om7ea/B737/docs/models/35-cabin-alt-diff-press-gauge.md

# 35. Cabin Alt / Diff Press Gauge

[📦 Download the printable model on MakerWorld](https://makerworld.com/en/models/3334561-boeing-737-overhead-cabin-alt-diff-press-gauge)

[← Back to model list](README.md)

---

> **Note**
> This gauge is a model of its own - it is not part of any panel model. **One** is needed for the complete project, on the **[Cabin Altitude Panel](36-cabin-altitude-panel.md)**.
>
> It is a **two-needle** instrument, and the largest gauge of the overhead. Both needles turn on the same axis, the short CABIN ALT needle on an acrylic pipe and the long DIFF PRESS needle on an acrylic rod running inside that pipe, and each one has a servo of its own.

---

## Photos

<table>
<tbody>
<tr>
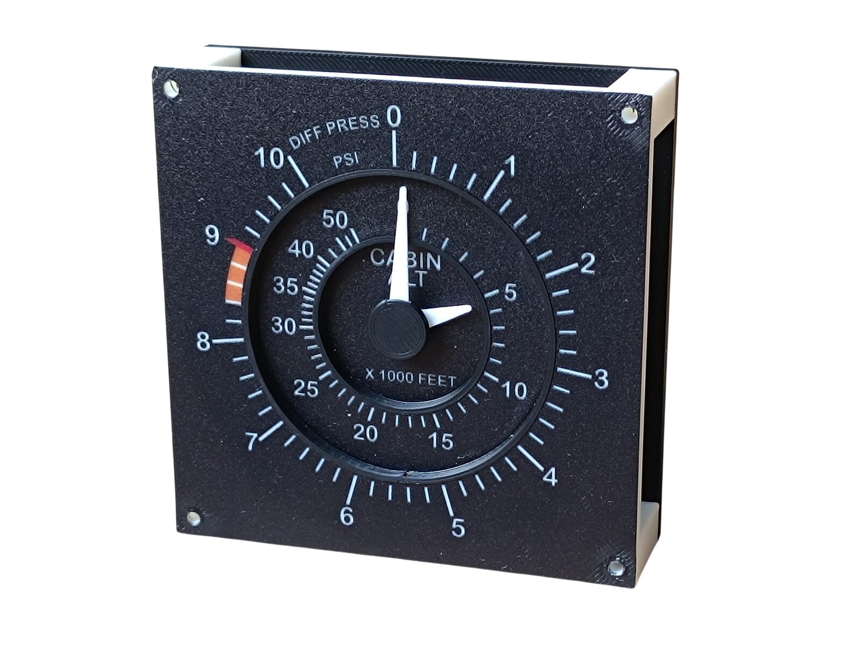
[picture p176: images/panels/35-cabin-alt-photo-1-front.jpg]
Finished Cabin Alt / Diff Press Gauge, front
<td align="center" width="50%"><br><sub>The finished gauge</sub></td>
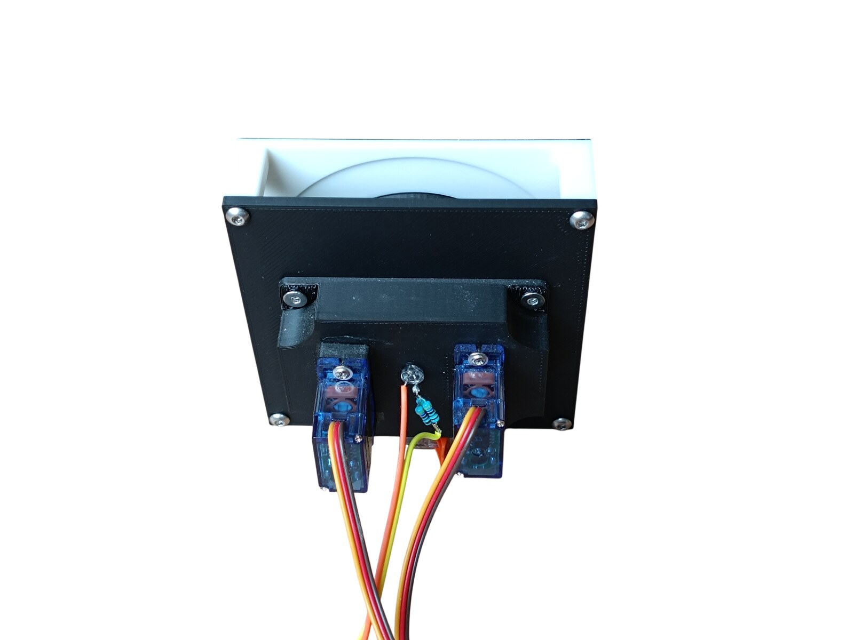
[picture p177: images/panels/35-cabin-alt-photo-2-rear.jpg]
The gauge from behind, showing the two servos on the gears cover and the resistor of the needle LED
<td align="center" width="50%"><br><sub>From behind - the two servos on the gears cover, with the resistor of the needle LED between them</sub></td>
</tr>
</tbody>
</table>

---

## How It Works

The dial is built from three printed faces, one behind the other, each with its own UV-printed scale: the square **outer** face carries the **DIFF PRESS** scale in psi, the **middle** ring the **CABIN ALT** scale in thousands of feet, and the **inner** disc the CABIN ALT lettering. A black shielding ring sits between each pair, so no light crosses from one face to the next.

Each needle is driven by its own **SG90 servo** through a pair of printed gears. The **18-tooth** gear sits on the servo and a **9-tooth** gear on the needle shaft, so a needle turns twice as far as its servo - the 180° of an SG90 cover the whole scale.

The two shafts run on the same axis, one inside the other. The **short needle**, the one that reads CABIN ALT, sits on a **3 mm acrylic pipe** turning in two **MR63ZZ** ball bearings, one in the inner part and one in the backlight part. The **long needle**, the one that reads DIFF PRESS, sits on a **2 mm acrylic rod** that runs down the middle of that pipe; at the back the rod turns in a single **MR52ZZ** bearing pressed into the pipe gear, and at the front the pipe itself guides it.

What keeps the two drives apart is height. The two servos sit at different depths in the gears cover, and the two gears on the shafts are different heights as well - the **3 mm pipe gear** and the **2 mm rod gear** - so each servo gear reaches only one of them.

Both shafts are light pipes too: a white LED in the gears cover shines up the rod and the pipe into the needles. The two gears at the back sit in that light path, which is why they are printed in **transparent** PLA.

The dial itself is lit separately, by two LED strips inside the backlight part - see [Backlight](#backlight).

---

## Filament

| | Colour | Filament |
|---|---|---|
|  | Transparent | Filament PM PLA Transparent |
|  | White | Bambu PLA Basic Jade White (10100) |
|  | Black | Bambu PLA Basic Black (10101) |

---

## 3D Printed Parts

| Qty | Part | Colour | Notes |
|---:|---|---|---|
| 1× | outer | White | the square face - the UV-printed DIFF PRESS scale goes on it and it diffuses the backlight |
| 1× | middle | White | the ring behind it, with the UV-printed CABIN ALT scale |
| 1× | inner | White | the disc at the centre, with the CABIN ALT lettering; carries the first MR63ZZ bearing |
| 1× | shielding outer+middle | Black | the ring wall between the outer and the middle face |
| 1× | shielding middle+inner | Black | the ring wall between the middle and the inner face |
| 1× | backlight | Black | the rear plate; carries the second MR63ZZ bearing |
| 1× | gears cover | Black | the bracket for the two servos |
| 1× | pipe gear (3 mm) | Transparent | 9 teeth, on the acrylic pipe; in the light path of the needle LED |
| 1× | rod gear (2 mm) | Transparent | 9 teeth, on the acrylic rod; in the light path of the needle LED |
| 2× | servo gear | Black | 18 teeth, on the servo shafts |
| 1× | long needle | White | the DIFF PRESS needle, on the acrylic rod |
| 1× | short needle | White | the CABIN ALT needle, on the acrylic pipe |
| 1× | needle cap | Black | covers the hub of the long needle |

All the parts print on a **Smooth** PEI plate.

---

## Electronic and Mechanical Components

| Qty | Part | Reference |
|---:|---|---|
| 2× | **Servo SG90** - 180°, plastic gears | [Product I used](../../images/parts/AE_servo_SG90.png) |
| 2× | **Ball bearing MR63ZZ** - 3 × 6 × 2.5 mm | [Product I used](../../images/parts/AE_bearing_MR63ZZ.png) |
| 1× | **Ball bearing MR52ZZ** - 2 × 5 × 2.5 mm | [Product I used](../../images/parts/AE_bearing_MR52ZZ.png) |
| 1× | **Acrylic pipe** - 2.1 × 3 × 200 mm, transparent; the shaft of the short needle is cut from it | [Product I used](../../images/parts/AE_acrylic_pipe.png) |
| 1× | **Acrylic rod** - 2 mm, transparent; the shaft of the long needle is cut from it | [Product I used](../../images/parts/AE_acrylic_rod.png) |
| 1× | **White 5 mm flat top LED** - the same one the annunciators use | [Product I used](../../images/parts/AE_led_white.png) |
| 1× | **150 Ω resistor** - in series with the white LED | |
| 2× | **LED strip** - the scale backlight | [Product I used](../../images/parts/AE_led_strip.png) |
| 1× | **820 Ω resistor** - in series with the two LED strips | |
| 2× | **Splice connector** - lever type, for the 12 V of the scale backlight | |

The screws that come with the servos are used as well: two hold each servo to the gears cover, and a third fastens its gear to the servo shaft.

---

## Screws

| Qty | Screw | Joins |
|---:|---|---|
| 4× | Dome head M3×8 | backlight + outer |
| 4× | Dome head M3×5 | gears cover + backlight |

---

## UV Print Files

| Qty | File |
|---:|---|
| 1× | A4 PDF - gauge scales |

Three of the scales on that sheet belong to this gauge: the large square **DIFF PRESS** face, the **CABIN ALT** ring with the numbers, and the small disc with the CABIN ALT lettering. The PDF and the printing instructions are on the [UV Print Files](../uv-print.md) page.

---

## Backlight

### Scale

The scale is lit by two LED strips inside the backlight part, one on each side, shining through the white outer, middle and inner parts from behind. They run on **12 V** taken from the backlighting of the [Cabin Altitude Panel](36-cabin-altitude-panel.md), so the gauge dims together with that panel - see [Power supply](../system-overview.md#power-supply).

The two strips are not wired straight across that 12 V: an **820 Ω resistor** goes in series with the pair. The white parts pass far more light than the printed face of a panel does, so on the bare supply the scale burns out much brighter than the lettering around it. The resistor holds it back to the brightness of the rest of the overhead.

The two strips sit in parallel and the resistor goes in the lead feeding them, close to the strips.

The two LED strips in parallel with the series resistor in the supply lead

### Needles

The needles have a light of their own: a white 5 mm LED in the gears cover, between the two servos, shining up through the transparent gears and on into the acrylic pipe and the acrylic rod. It runs on **5 V** with a **150 Ω** resistor in series, and it lights both needles at once.

> **Note**
> The needle lighting works, but the effect is weak. White PLA does not carry light well over the length of a needle, so a needle glows rather than lights up. It is worth building - but do not expect the needles to stand out the way the scale does.

---

## Wiring

The gauge has four connections.

| Connection | Supply | Comes from |
|---|---|---|
| CABIN ALT needle servo | 5 V | the control signal, **+5 V** and **GND**, all three from the pin headers at **pin 7** of the [RJ45 Direct](../pcb/rj45-direct.md) PCB on the **[Cabin Altitude Panel](36-cabin-altitude-panel.md)** - socket **D3** on **Overhead_4** |
| DIFF PRESS needle servo | 5 V | the same three, from the pin headers at **pin 6** of that board |
| Needle LED | 5 V | **+5 V** and **GND** from a two-pin header on that same board - see [the modified board](36-cabin-altitude-panel.md#the-modified-board). The pair runs through a **150 Ω** resistor - see [Backlight](#backlight) |
| Scale backlight | 12 V | the backlighting of the Cabin Altitude Panel, through an **820 Ω** resistor - see [Backlight](#backlight) |

> **⚠️ Both servo plugs have to be rewired**\
> The SG90 does not leave the factory in the order the RJ45 Direct PCB expects, so a servo will **not** work if you plug it in as it comes. **Swap the red and the yellow wire:**
>
> | | Wire order in the plug |
> |---|---|
> | As delivered | brown - red - yellow |
> | **Needed** | **brown - yellow - red** |
>
> Lift the small tabs on the plastic housing, pull those two crimped contacts out and swap them over. Brown stays where it is. (On some SG90s the yellow wire is orange instead - it is the signal wire either way.)

The 12 V for the scale backlight is brought over from the panel's own backlighting with two **lever-type splice connectors**, one for +12 V and one for GND. Where they sit is up to you - both on the gauge works fine, and so does one on the gauge and one on the panel. There is nothing to screw them to, so **glue them down with super glue.**

---

## Assembly

Screw abbreviations used below: **DH** = dome head.

<table>
<tbody>
<tr>
<td width="55%"><b>1.</b> Screw the two servos to the <b>gears cover</b> with the screws that come in the servo bags, two per servo.</td>
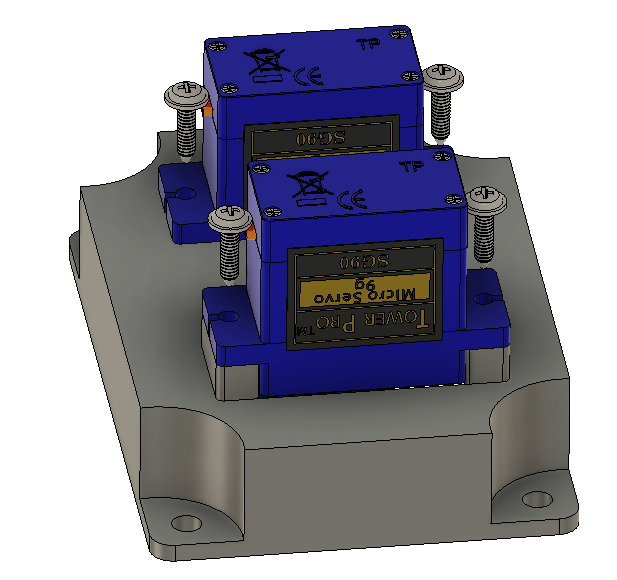
[picture p178: images/panels/35-cabin-alt-step-01.png]
The two servos screwed to the gears cover
<td align="center"></td>
</tr>
</tbody>
<tbody>
<tr>
<td width="55%"><b>2.</b> Fasten an 18-tooth <b>servo gear</b> to each servo, again with a screw from the servo bag.</td>
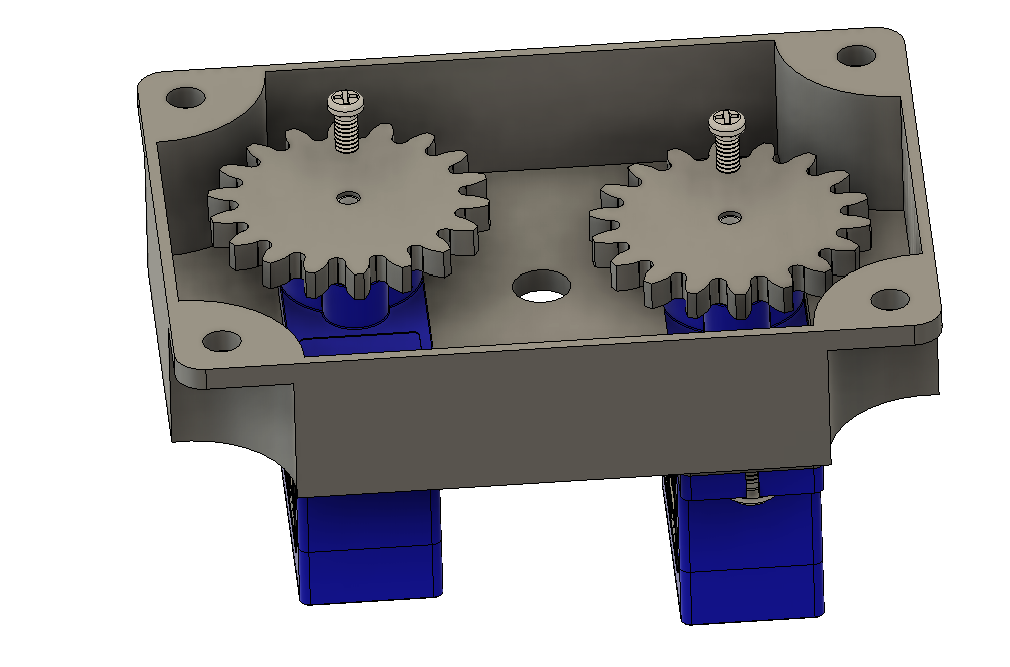
[picture p179: images/panels/35-cabin-alt-step-02.png]
The 18-tooth gears fastened to the servo shafts
<td align="center"></td>
</tr>
</tbody>
<tbody>
<tr>
<td width="55%"><b>3.</b> Stick the printed foil with the <b>DIFF PRESS</b> scale onto the <b>outer</b> part.</td>
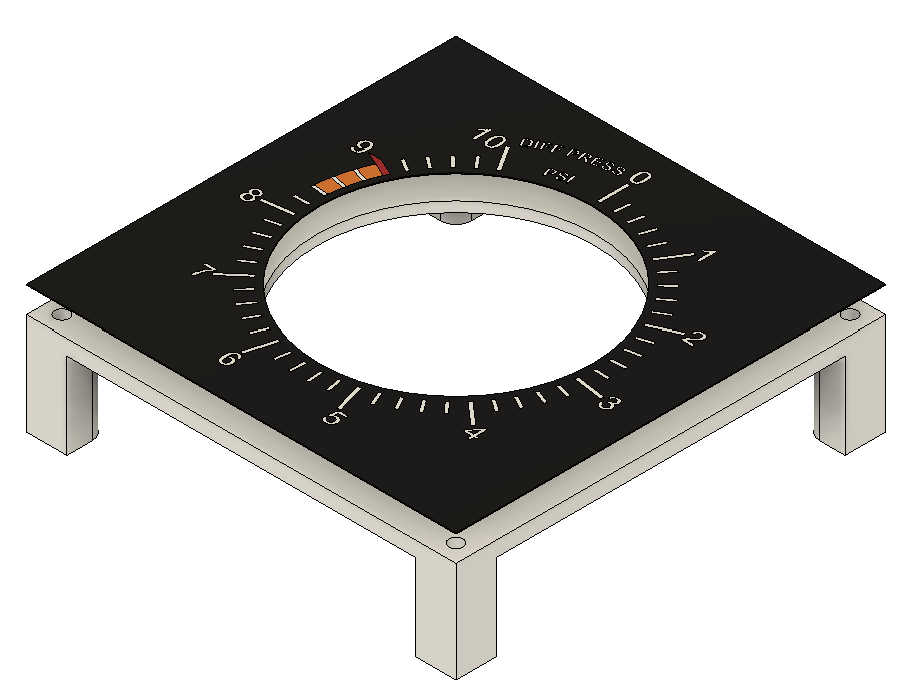
[picture p180: images/panels/35-cabin-alt-step-03.png]
The DIFF PRESS foil stuck onto the outer part
<td align="center"></td>
</tr>
</tbody>
<tbody>
<tr>
<td width="55%"><b>4.</b> Stick the printed foil with the <b>CABIN ALT</b> scale onto the <b>middle</b> part.</td>
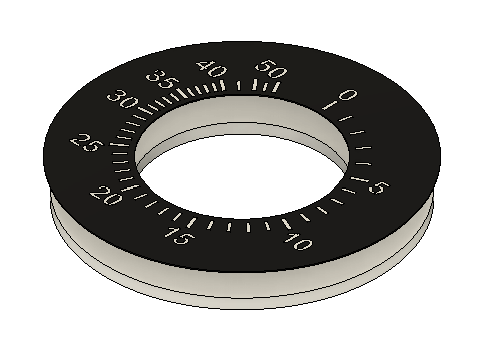
[picture p181: images/panels/35-cabin-alt-step-04.png]
The CABIN ALT scale foil stuck onto the middle part
<td align="center"></td>
</tr>
</tbody>
<tbody>
<tr>
<td width="55%"><b>5.</b> Stick the printed foil with the CABIN ALT lettering onto the <b>inner</b> part.</td>
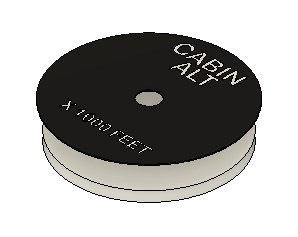
[picture p182: images/panels/35-cabin-alt-step-05.png]
The lettering foil stuck onto the inner part
<td align="center"></td>
</tr>
</tbody>
<tbody>
<tr>
<td width="55%"><b>6.</b> Drop the <b>shielding outer+middle</b> part into the outer part.</td>
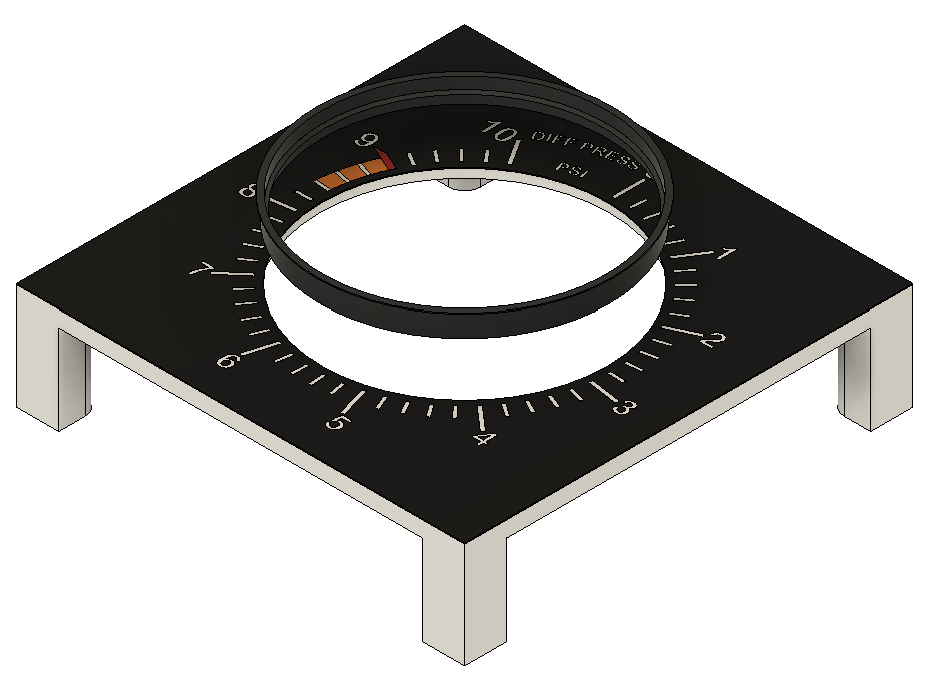
[picture p183: images/panels/35-cabin-alt-step-06.png]
The outer shielding ring dropped into the outer part
<td align="center"></td>
</tr>
</tbody>
<tbody>
<tr>
<td width="55%"><b>7.</b> Drop the <b>middle</b> part into that shielding.</td>
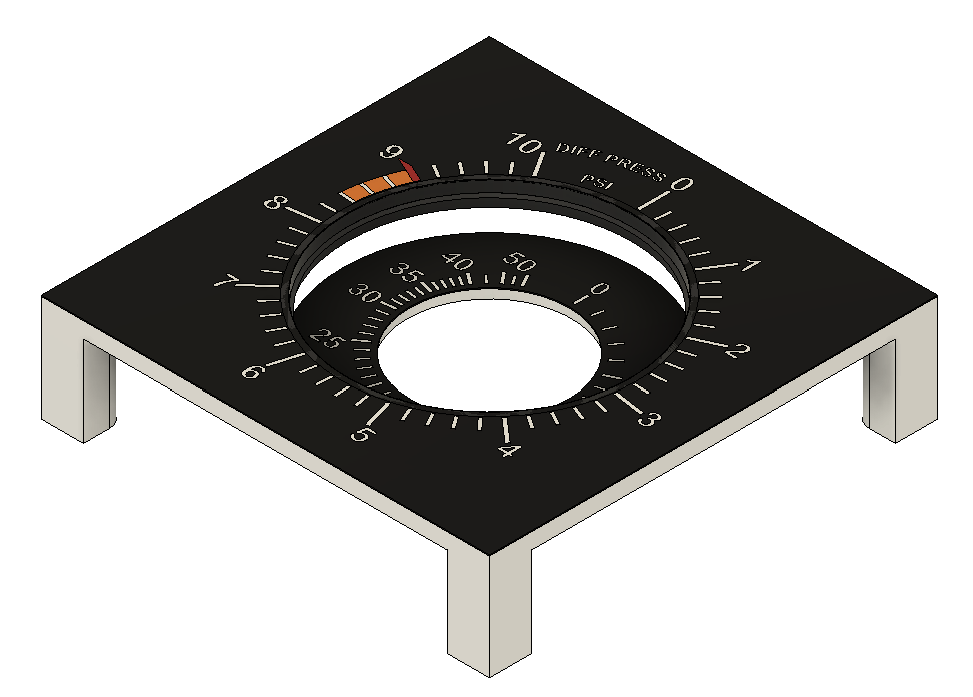
[picture p184: images/panels/35-cabin-alt-step-07.png]
The middle part dropped into the outer shielding ring
<td align="center"></td>
</tr>
</tbody>
<tbody>
<tr>
<td width="55%"><b>8.</b> Drop the <b>shielding middle+inner</b> part in next.</td>
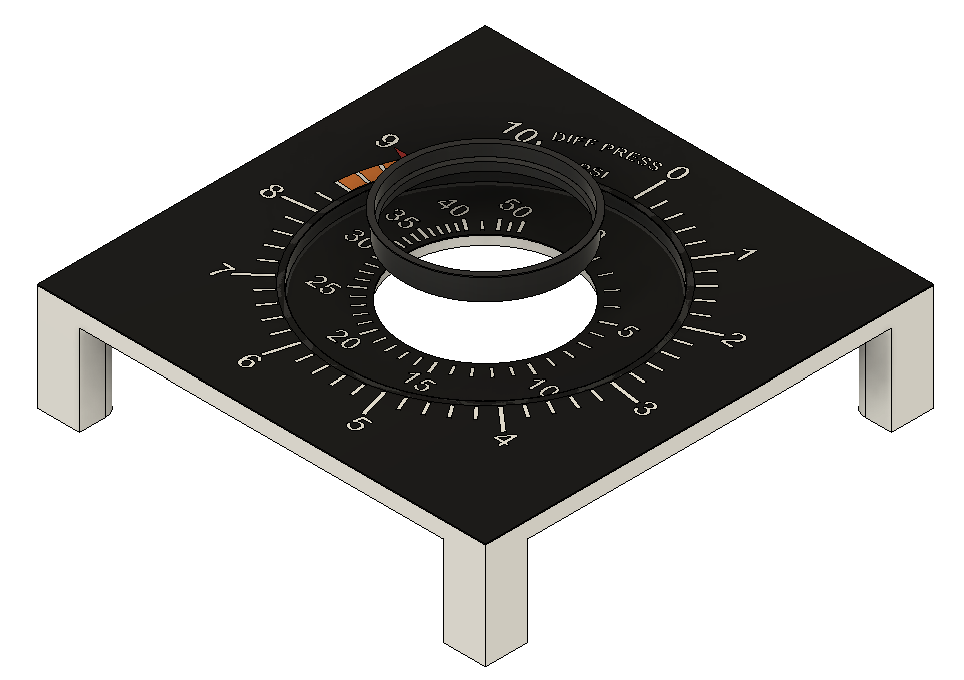
[picture p185: images/panels/35-cabin-alt-step-08.png]
The inner shielding ring dropped in
<td align="center"></td>
</tr>
</tbody>
<tbody>
<tr>
<td width="55%"><b>9.</b> Drop the <b>inner</b> part into it.</td>
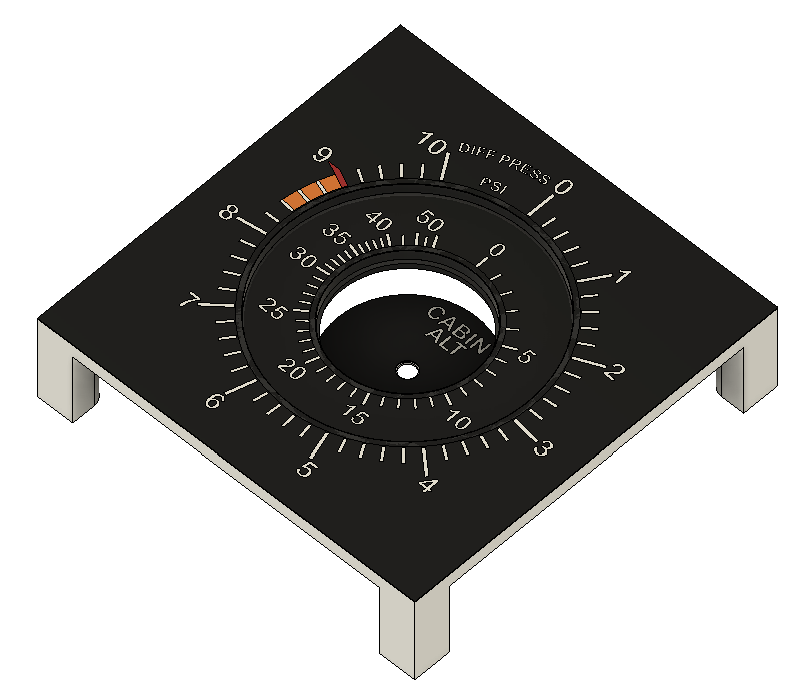
[picture p186: images/panels/35-cabin-alt-step-09.png]
The inner part dropped into the inner shielding ring
<td align="center"></td>
</tr>
</tbody>
<tbody>
<tr>
<td width="55%"><b>10.</b> Press the first <b>MR63ZZ</b> bearing into the inner part, from the back.</td>
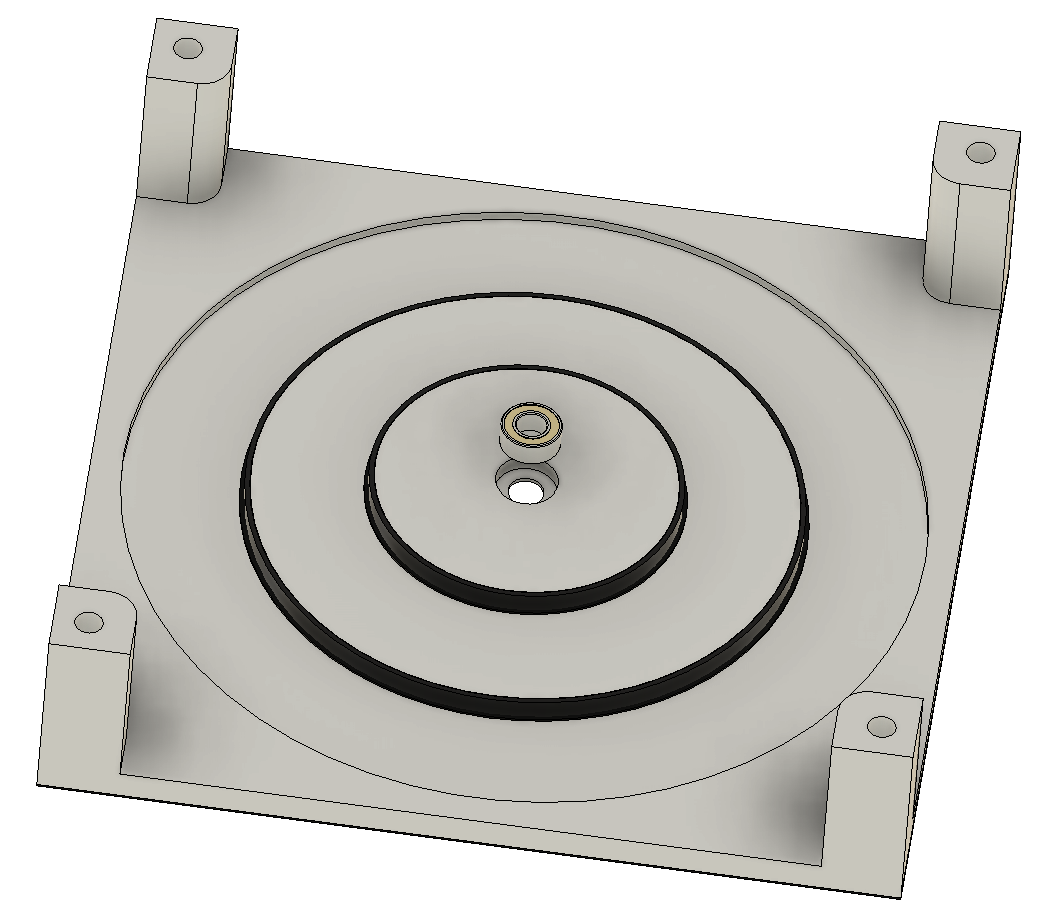
[picture p187: images/panels/35-cabin-alt-step-10.png]
The first MR63ZZ bearing pressed into the inner part
<td align="center"></td>
</tr>
</tbody>
<tbody>
<tr>
<td width="55%"><b>11.</b> Fit the two <b>LED strips</b> into the <b>backlight</b> part and bring their leads out. The two are wired in parallel and the <b>820 Ω resistor</b> goes in the lead feeding them - see <a href="#backlight">Backlight</a>. They have to go in before the part is screwed on in the next step.</td>
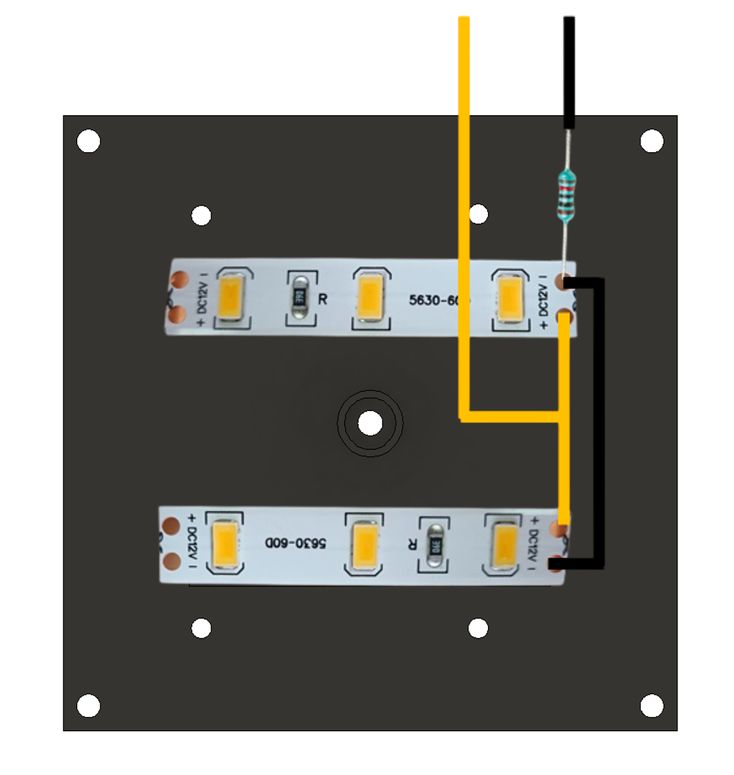
[picture p188: images/panels/35-cabin-alt-backlight-leds.png]
The two LED strips on the backlight part, wired in parallel with the series resistor
<td align="center"></td>
</tr>
</tbody>
<tbody>
<tr>
<td width="55%"><b>12.</b> Screw the <b>backlight</b> part on with 4× DH M3×8.</td>
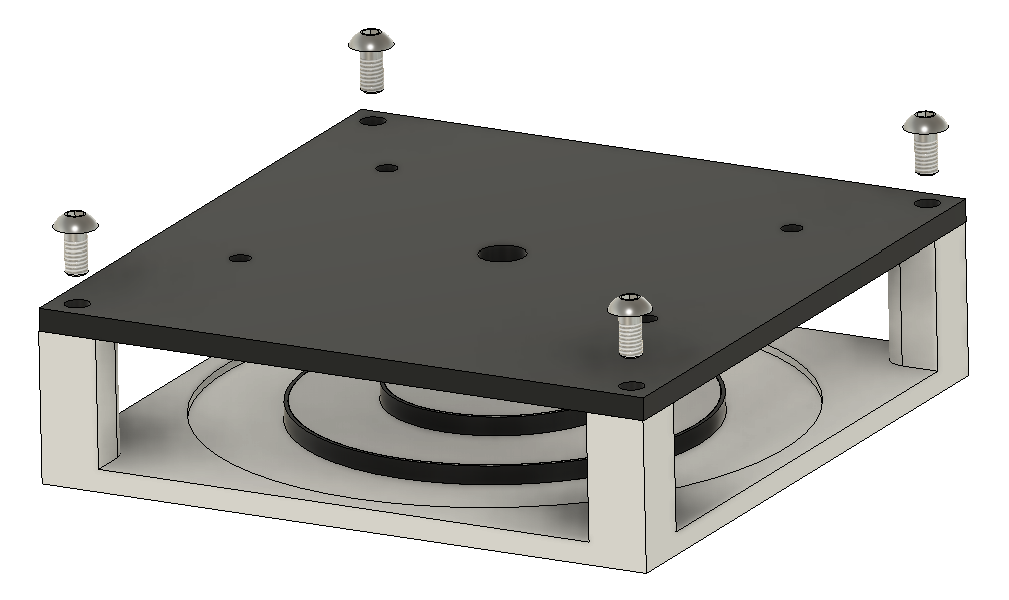
[picture p189: images/panels/35-cabin-alt-step-12.png]
The backlight part screwed on with four M3x8 screws
<td align="center"></td>
</tr>
</tbody>
<tbody>
<tr>
<td width="55%"><b>13.</b> Press the second <b>MR63ZZ</b> bearing into the backlight part.</td>
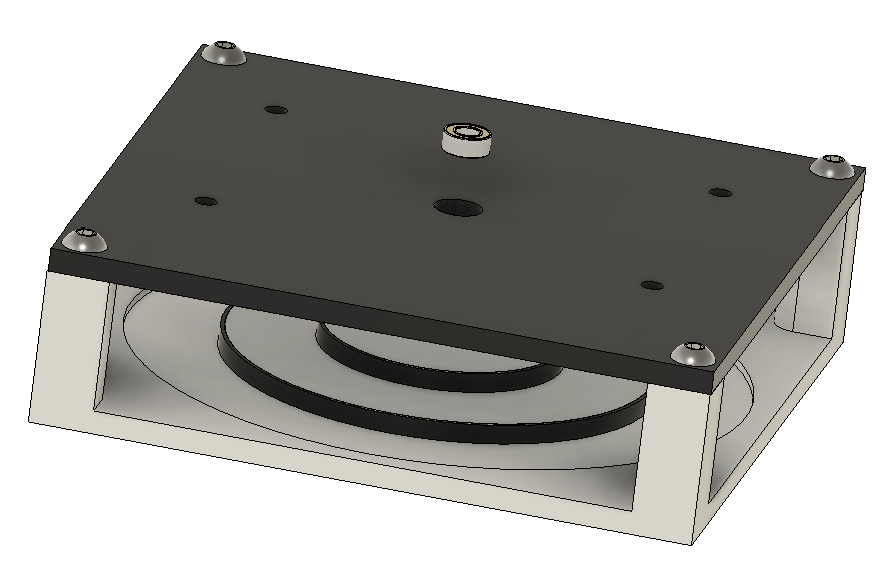
[picture p190: images/panels/35-cabin-alt-step-13.png]
The second MR63ZZ bearing pressed into the backlight part
<td align="center"></td>
</tr>
</tbody>
<tbody>
<tr>
<td width="55%"><b>14.</b> Push the <b>acrylic pipe</b> through both bearings. If it will not go, warm it with a hair dryer to soften it slightly. I used a 23.5 mm length.</td>
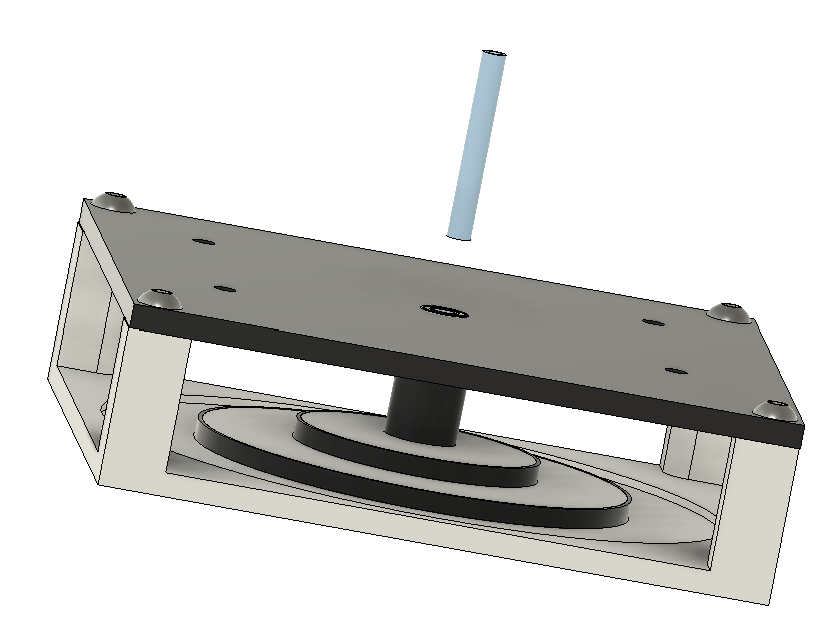
[picture p191: images/panels/35-cabin-alt-step-14.png]
The acrylic pipe pushed through both bearings
<td align="center"></td>
</tr>
</tbody>
<tbody>
<tr>
<td width="55%"><b>15.</b> From the front, glue the <b>short needle</b> - the CABIN ALT one - onto the pipe with super glue.</td>
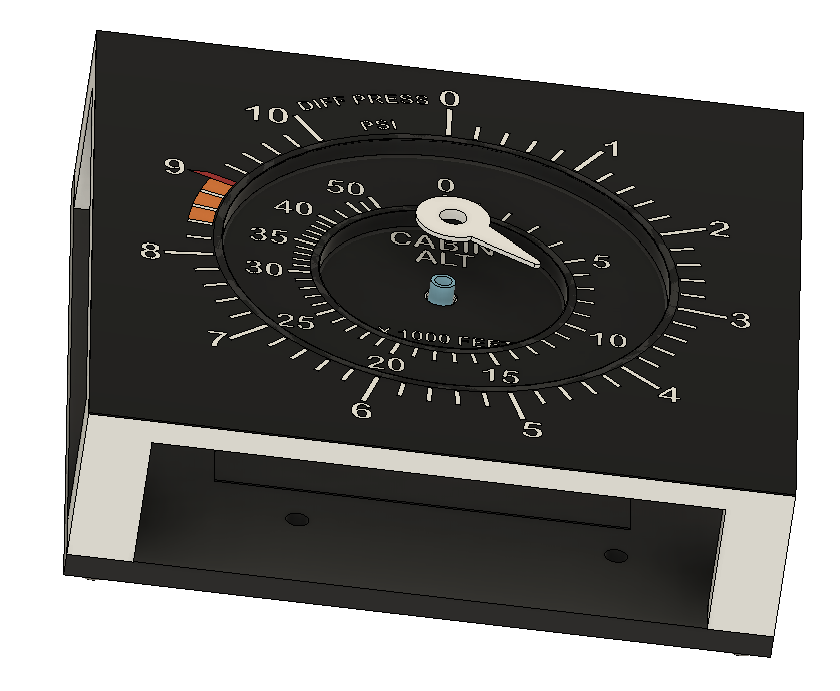
[picture p192: images/panels/35-cabin-alt-step-15.png]
The short needle glued onto the acrylic pipe from the front
<td align="center"></td>
</tr>
</tbody>
<tbody>
<tr>
<td width="55%"><b>16.</b> From the back, glue the <b>pipe gear</b> - 9 teeth, 3 mm high - onto the acrylic pipe.</td>
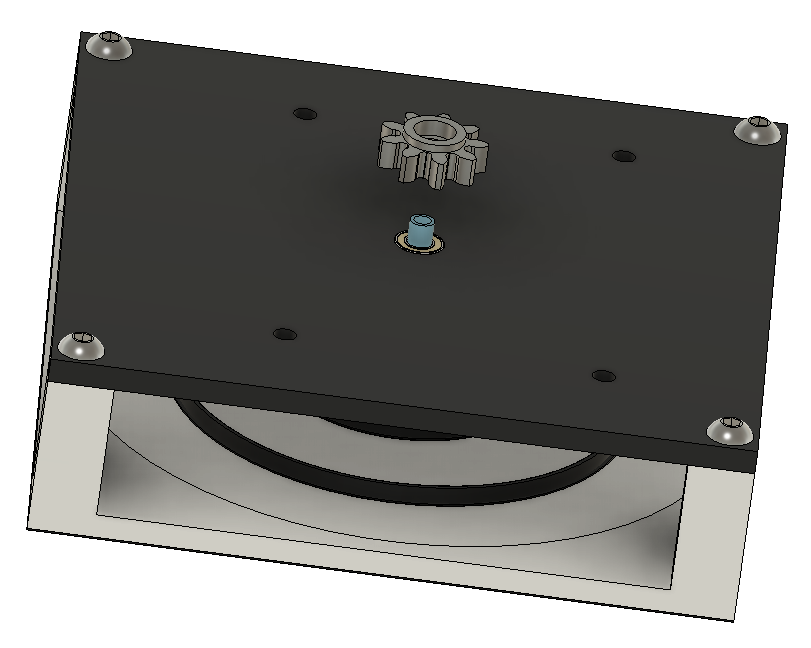
[picture p193: images/panels/35-cabin-alt-step-16.png]
The 3 mm pipe gear glued onto the acrylic pipe from the back
<td align="center"></td>
</tr>
</tbody>
<tbody>
<tr>
<td width="55%"><b>17.</b> Press the <b>MR52ZZ</b> bearing into the pipe gear.</td>
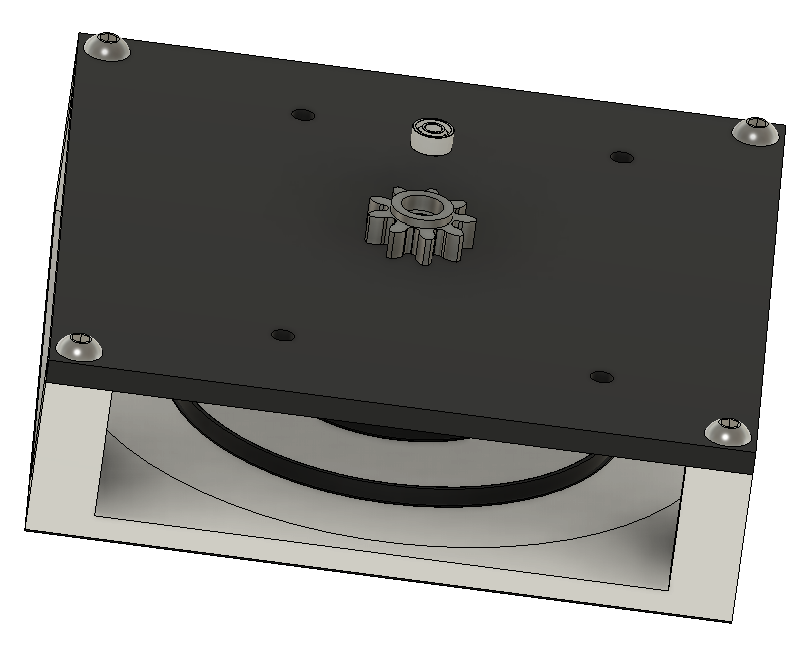
[picture p194: images/panels/35-cabin-alt-step-17.png]
The MR52ZZ bearing pressed into the pipe gear
<td align="center"></td>
</tr>
</tbody>
<tbody>
<tr>
<td width="55%"><b>18.</b> Push the <b>acrylic rod</b> through the MR52ZZ bearing and on down the inside of the pipe. I used 30.5 mm, but it is safer to cut it to length once it is in place.</td>
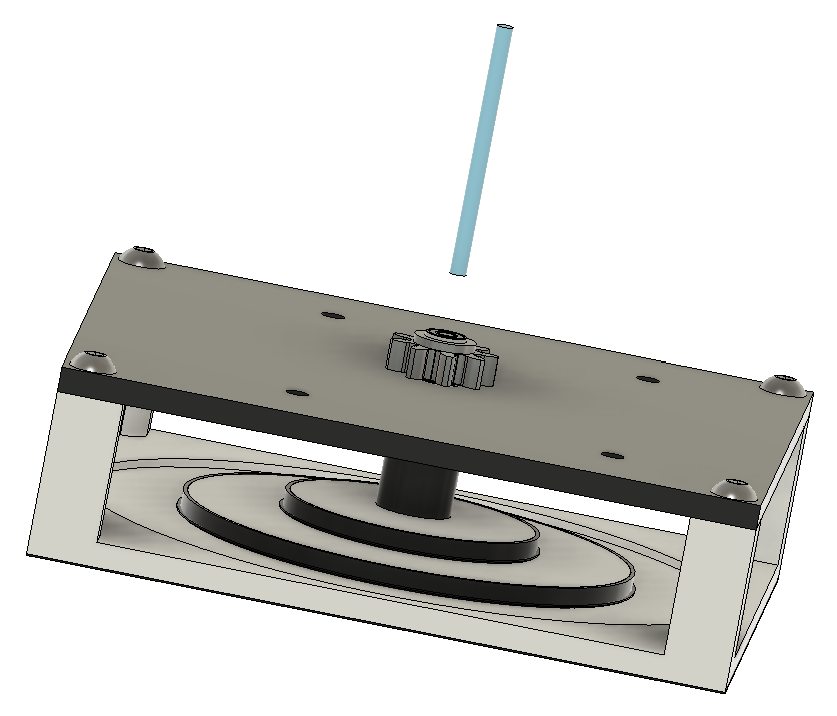
[picture p195: images/panels/35-cabin-alt-step-18.png]
The acrylic rod pushed through the bearing into the pipe
<td align="center"></td>
</tr>
</tbody>
<tbody>
<tr>
<td width="55%"><b>19.</b> From the front, glue the <b>long needle</b> - the DIFF PRESS one - onto the rod.</td>
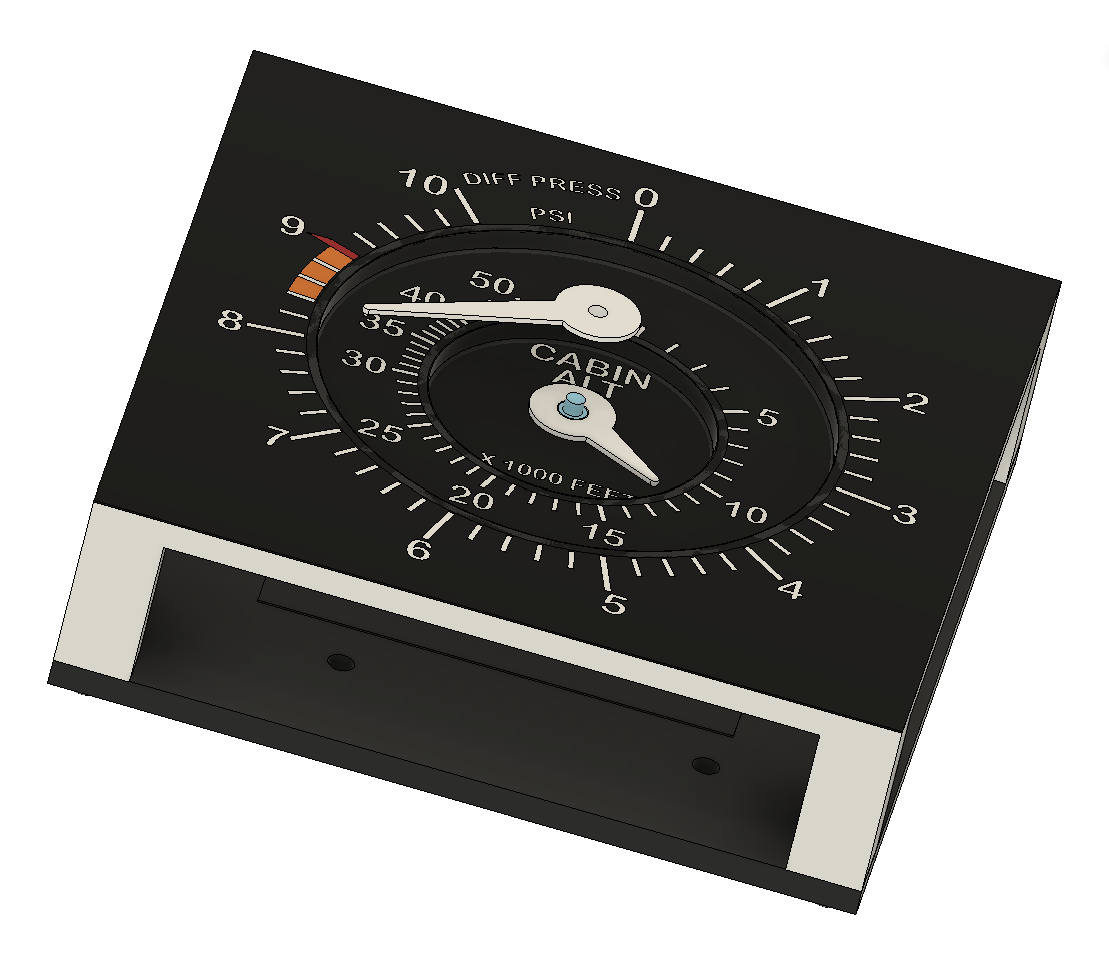
[picture p196: images/panels/35-cabin-alt-step-19.png]
The long needle glued onto the acrylic rod from the front
<td align="center"></td>
</tr>
</tbody>
<tbody>
<tr>
<td width="55%"><b>20.</b> Glue the black <b>needle cap</b> onto the hub of the long needle.</td>
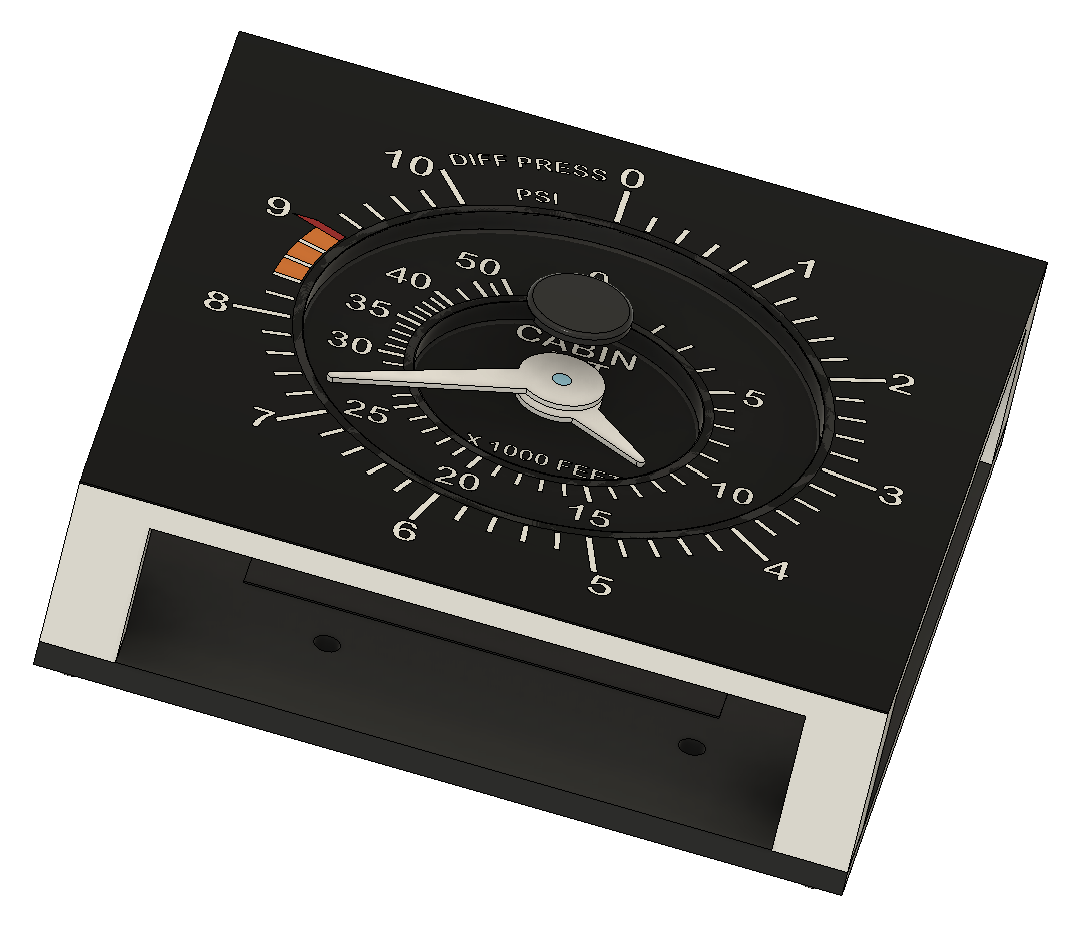
[picture p197: images/panels/35-cabin-alt-step-20.png]
The black cap glued onto the hub of the long needle
<td align="center"></td>
</tr>
</tbody>
<tbody>
<tr>
<td width="55%"><b>21.</b> Glue the <b>rod gear</b> - 9 teeth, 2 mm high - onto the acrylic rod.</td>
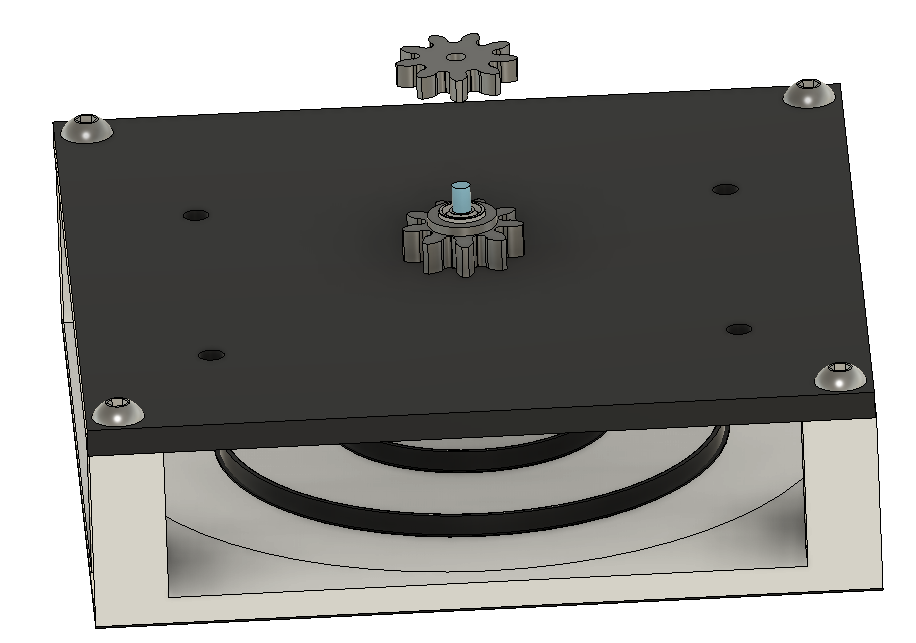
[picture p198: images/panels/35-cabin-alt-step-21.png]
The 2 mm rod gear glued onto the acrylic rod
<td align="center"></td>
</tr>
</tbody>
<tbody>
<tr>
<td width="55%"><b>22.</b> Put the gears cover with its two servos in place and screw it down with 4× DH M3×5.</td>
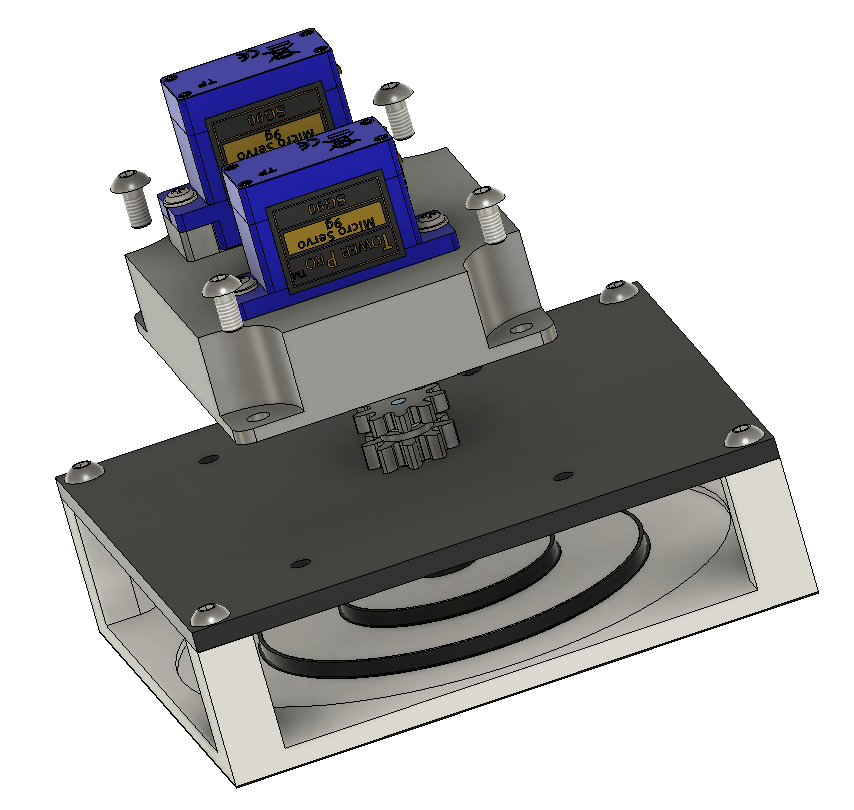
[picture p199: images/panels/35-cabin-alt-step-22.png]
The gears cover with both servos screwed onto the backlight part
<td align="center"></td>
</tr>
</tbody>
<tbody>
<tr>
<td width="55%"><b>23.</b> Push the white <b>LED</b> - the one with the 150 Ω resistor - into the hole between the two servos.</td>
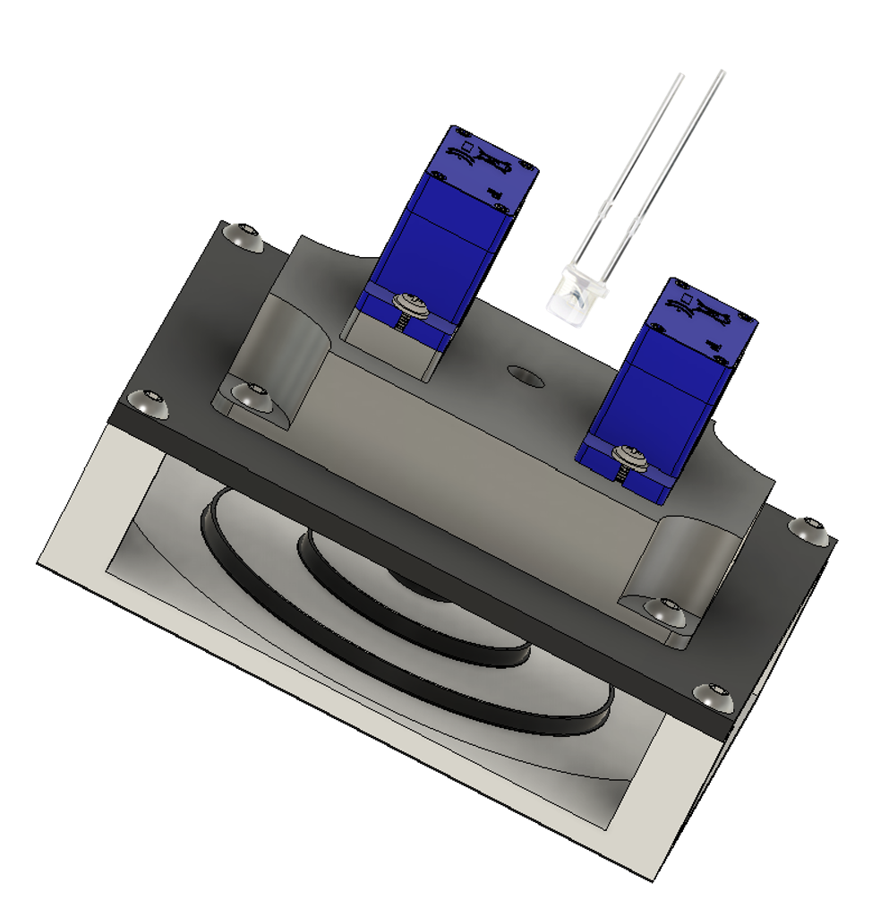
[picture p200: images/panels/35-cabin-alt-step-23.png]
The white LED pushed into the hole between the two servos
<td align="center"></td>
</tr>
</tbody>
</table>
