om7ea/B737/docs/pcb/cabin-pressure-display.md

# 9. Cabin Pressure Display

<table>
<tbody>
<tr>
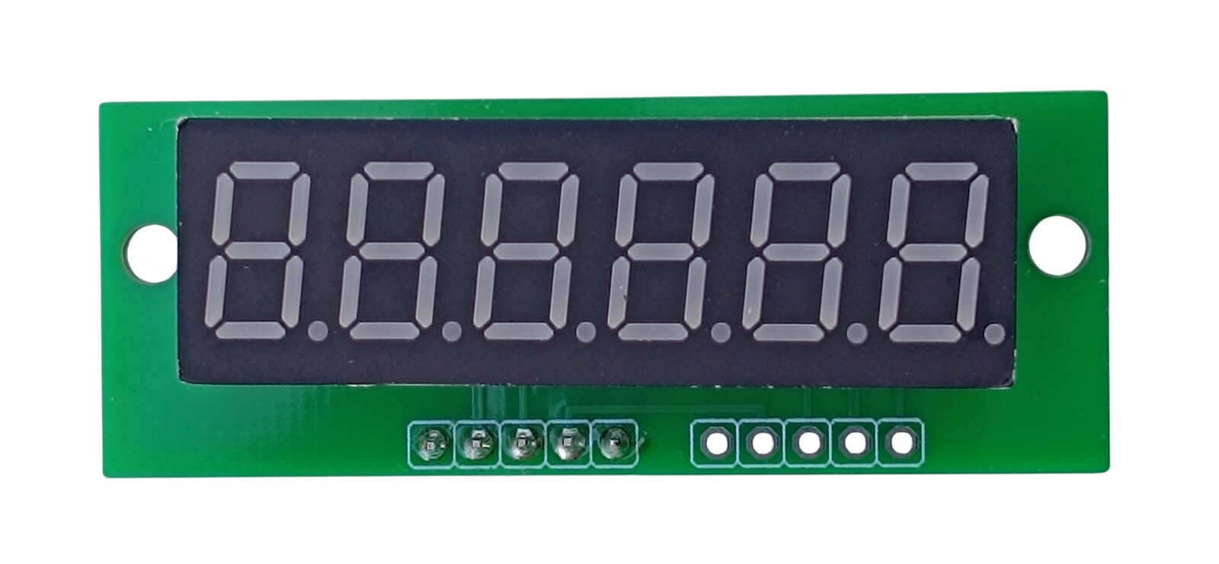
[picture p232: images/pcb/PCB_Cabin_Pressure_Display_top.jpg]
Cabin Pressure Display - assembled module, top
<td align="center"><br><sub>Assembled module - top</sub></td>
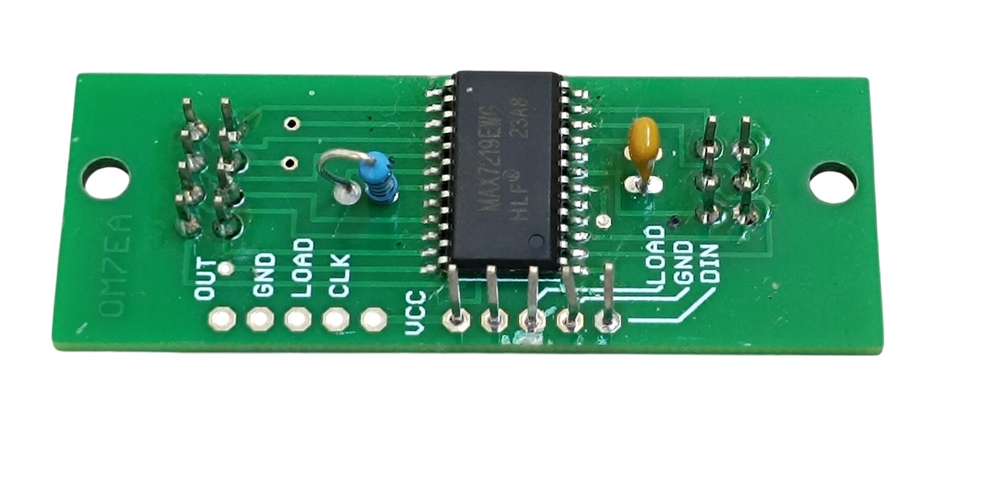
[picture p233: images/pcb/PCB_Cabin_Pressure_Display_bottom.jpg]
Cabin Pressure Display - assembled module, bottom
<td align="center"><br><sub>Assembled module - bottom</sub></td>
</tr>
</tbody>
<tbody>
<tr>
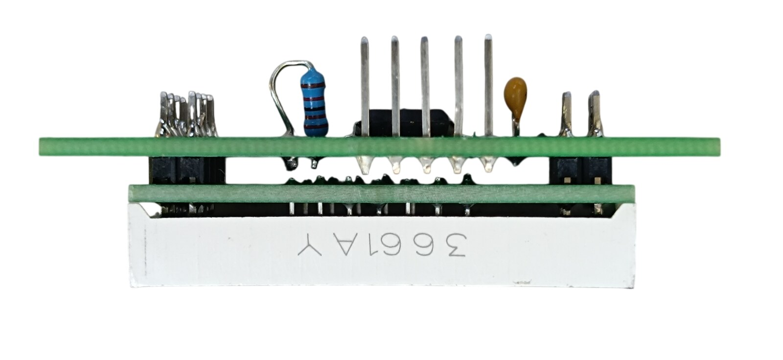
[picture p234: images/pcb/PCB_Cabin_Pressure_Display_side.jpg]
Cabin Pressure Display - the two boards seen from the side
<td align="center"><br><sub>The two boards from the side</sub></td>
<td align="center">Two Cabin Pressure Display modules joined by the Dupont cable<br><sub>Both modules joined</sub></td>
</tr>
</tbody>
</table>

[📥 Download Gerber files - board 1, PCB_Cabin_Pressure_Display_LED.zip](https://raw.githubusercontent.com/om7ea/B737/main/PCB/PCB_Cabin_Pressure_Display_LED.zip)

[📥 Download Gerber files - board 2, PCB_Cabin_Pressure_Display_MAX.zip](https://raw.githubusercontent.com/om7ea/B737/main/PCB/PCB_Cabin_Pressure_Display_MAX.zip)

[← Back to PCB overview](README.md)

---

## Purpose

Designed for the **[Cabin Pressure Control Panel](../models/32-cabin-pressure-control-panel.md)**. One module drives one six-digit display of that panel, and the panel carries two of them - FLT ALT and LAND ALT. The digits are driven by a **MAX7219**, the same driver as on the [AC and DC Meter](ac-dc-meter.md) board.

This is **two boards soldered into a single module**. Board 1 carries the display, board 2 carries the MAX7219, and the two double row pin headers that join them are soldered into both boards - the module cannot be taken apart again. Each board has its own outline and its own Gerber file, so both have to be ordered.

## Quantity

**2** modules are required for the complete project, which means **2× board 1 and 2× board 2**.

---

## Board 1 - Display

<table>
<tbody>
<tr>
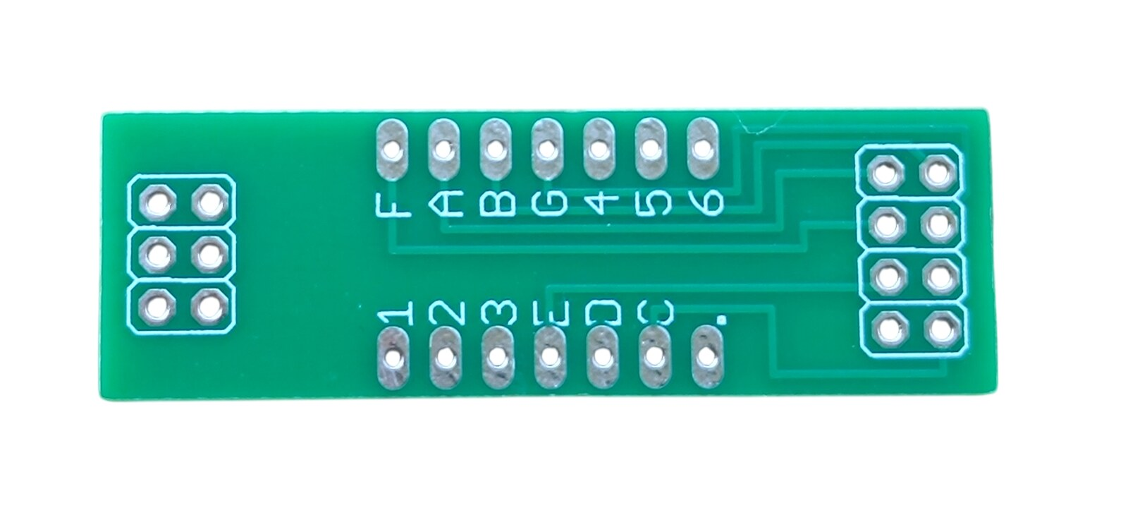
[picture p235: images/pcb/PCB_Cabin_Pressure_Display_led_top.jpg]
Cabin Pressure Display board 1 - display side
<td align="center"><br><sub>Display side</sub></td>
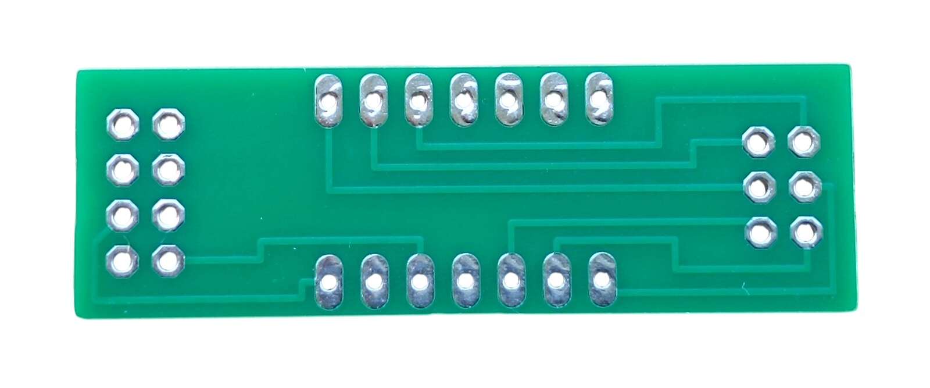
[picture p236: images/pcb/PCB_Cabin_Pressure_Display_led_bottom.jpg]
Cabin Pressure Display board 1 - reverse side
<td align="center"><br><sub>Reverse side</sub></td>
</tr>
</tbody>
</table>

The board carries nothing but the display and the two headers that reach board 2.

| Qty | Part | Reference |
|---:|---|---|
| 1× | **6-digit 7-segment display** - 0.36 inch, common cathode, yellow (3661AY) | [Product I used](../../images/parts/AE_6digit_display.png) |
| 1× | **Double row pin header 2×3** | |
| 1× | **Double row pin header 2×4** | |

> **Note**
> Solder both headers in first and the display only after that. The display sits over their solder joints, and once it is in place they cannot be reached.

---

## Board 2 - MAX7219 driver

<table>
<tbody>
<tr>
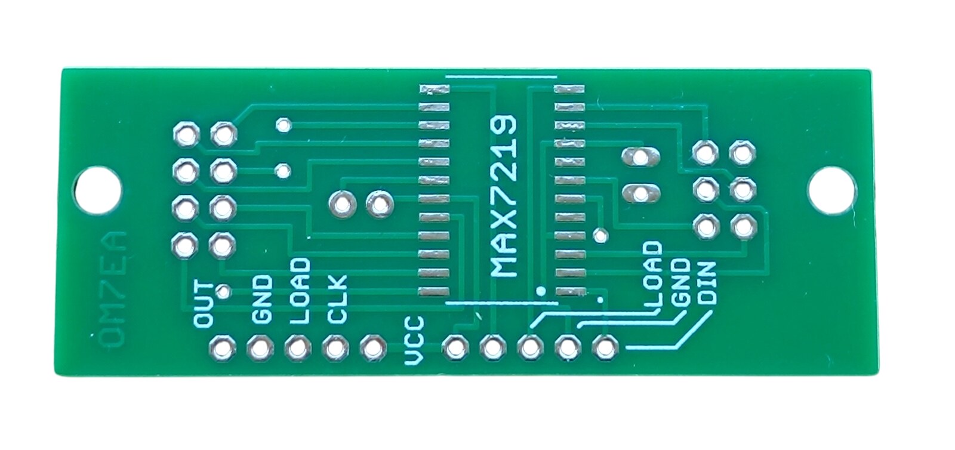
[picture p237: images/pcb/PCB_Cabin_Pressure_Display_max_bottom.jpg]
Cabin Pressure Display board 2 - component side
<td align="center"><br><sub>Component side</sub></td>
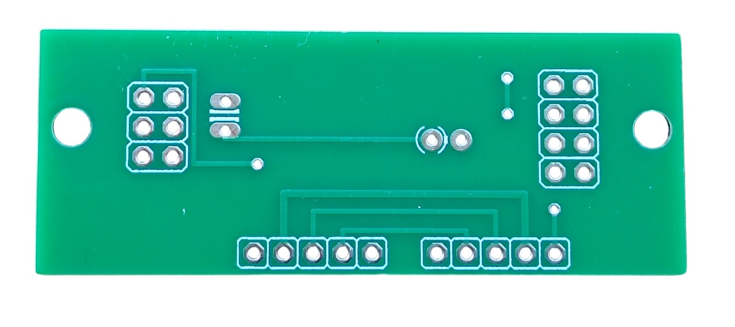
[picture p238: images/pcb/PCB_Cabin_Pressure_Display_max_top.jpg]
Cabin Pressure Display board 2 - reverse side
<td align="center"><br><sub>Reverse side</sub></td>
</tr>
</tbody>
</table>

| Qty | Part | Reference |
|---:|---|---|
| 1× | **MAX7219EWG** - SOP24, surface mount | [Product I used](../../images/parts/AE_MAX7219.png) |
| 1× | **22 kΩ resistor** | |
| 1× | **100 nF ceramic capacitor** | |
| 1× | **5-pin single row pin header** | |

The MAX7219 is the only surface mounted part. Solder it first, while the board still lies flat.

---

## Connections

Board 2 has two five-pad connectors, an input and an output, and the silkscreen names every pad:

| Connector | Pads, in the order they are printed on the board |
|---|---|
| Input | VCC, CLK, LOAD, GND, DIN |
| Output | OUT, GND, LOAD, CLK, VCC |

**Only one of the two is populated on each module**, so the two modules are not built the same way.

The FLT ALT module is the one the signal arrives at. Its five wires are soldered straight into the input pads - there is no connector - and they run to the RJ45 Direct PCB on the [Cabin Pressure Control Panel](../models/32-cabin-pressure-control-panel.md#wiring). Its five-pin header goes on the **output**.

| Input pad | Wire colour on my board |
|---|---|
| VCC | red |
| CLK | yellow |
| LOAD | brown |
| GND | black |
| DIN | white |

The LAND ALT module is fed from the first one, so its five-pin header goes on the **input** and its output stays empty. The two are joined by a 5-pin Dupont female to female cable, 10 cm long, signal for signal:

| Output pad - FLT ALT | Input pad - LAND ALT |
|---|---|
| OUT | DIN |
| GND | GND |
| LOAD | LOAD |
| CLK | CLK |
| VCC | VCC |

| Qty | Part | Reference |
|---:|---|---|
| 1× | **5-pin Dupont cable** - 2.54 mm, female to female, 10 cm | [Product I used](../../images/parts/AE_dupont_5p.png) |

> **Note**
> The wire colours of the Dupont cable mean nothing here - they do not follow the colours used anywhere else in this project. Go by the pad names printed on the boards, or by the photo of the two joined modules above.

---

## Schematic

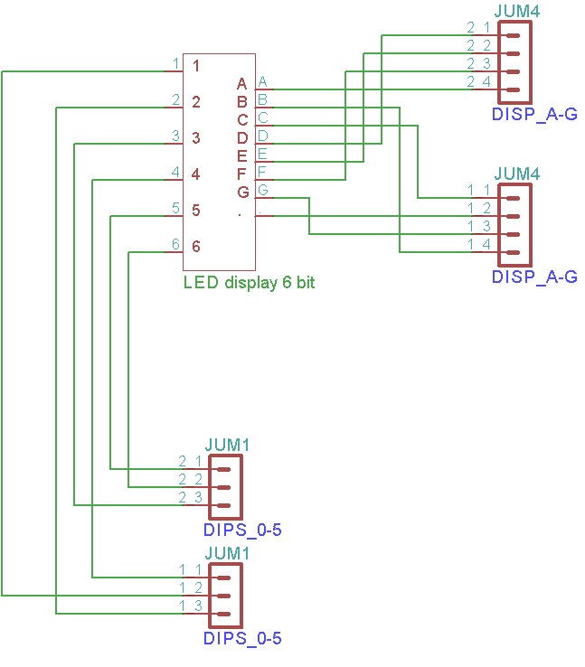
[picture p239: images/pcb/PCB_Cabin_Pressure_Display_LED_schematic.png]
Cabin Pressure Display board 1 schematic
<br><sub>Board 1 - Display</sub>

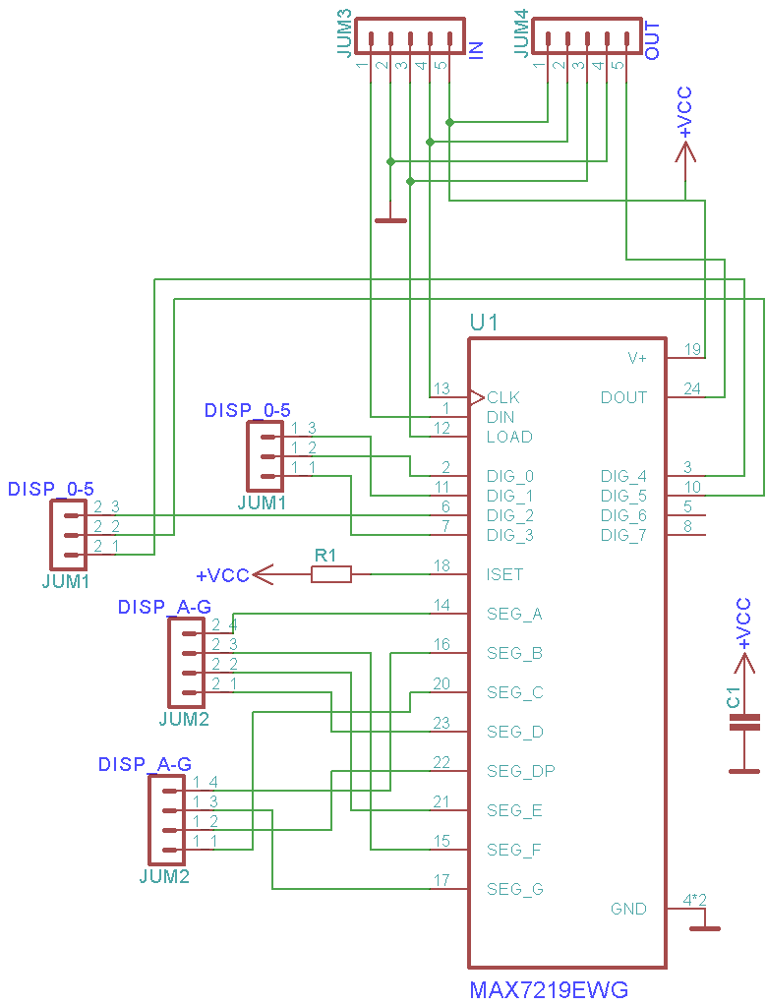
[picture p240: images/pcb/PCB_Cabin_Pressure_Display_MAX_schematic.png]
Cabin Pressure Display board 2 schematic
<br><sub>Board 2 - MAX7219 driver</sub>
