om7ea/B737/docs/models/27-interphone-and-dome-panel.md

# 27. Interphone and Dome Panel

[📦 Download the printable model on MakerWorld](https://makerworld.com/en/models/3309341-boeing-737-overhead-interphone-and-dome-panel)

[← Back to model list](README.md)

---

## Photos

<table>
<tbody>
<tr>
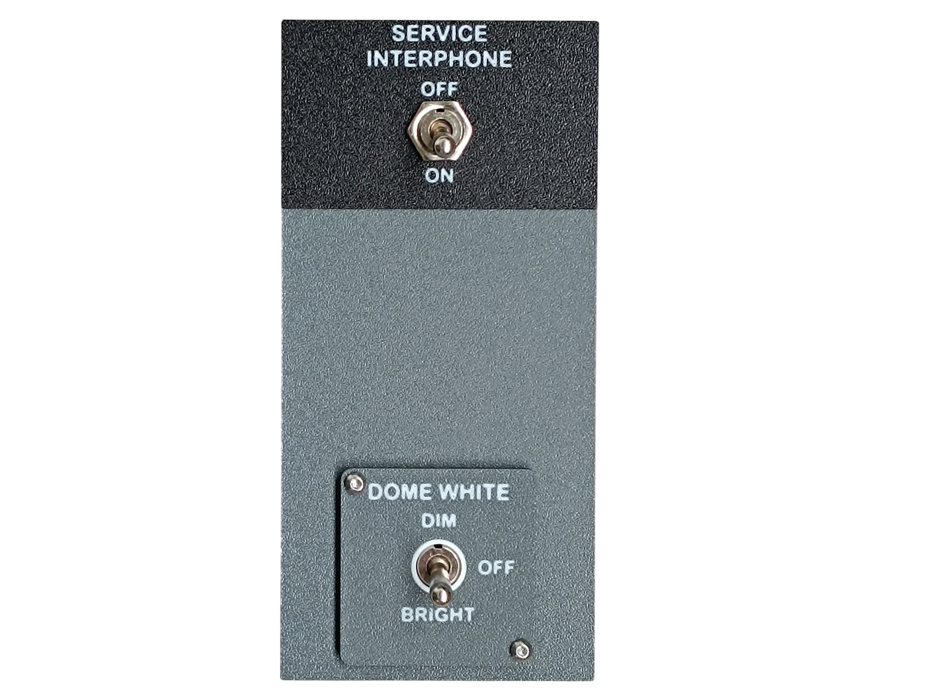
[picture p279: images/panels/27-interphone-dome-photo-1-front.jpg]
Finished Interphone and Dome Panel, front
<td align="center" width="50%"><br><sub>Finished panel</sub></td>
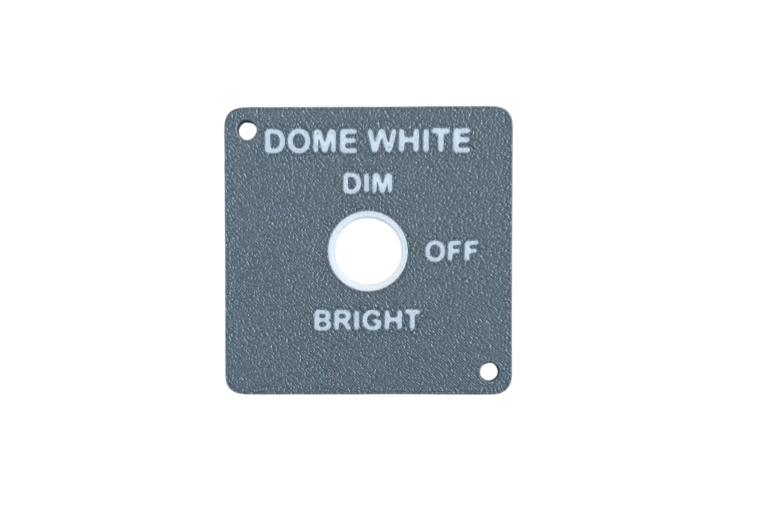
[picture p280: images/panels/27-interphone-dome-photo-2-top-panel.jpg]
The printed top panel
<td align="center" width="50%"><br><sub>The top panel - the DOME WHITE plate, Dark Gray with the lettering in Jade White</sub></td>
</tr>
</tbody>
<tbody>
<tr>
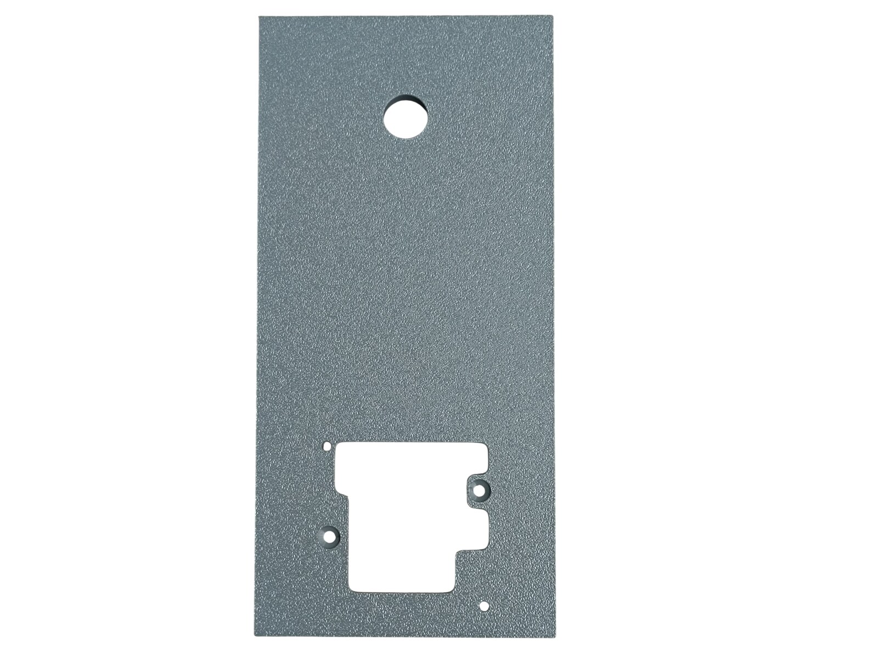
[picture p281: images/panels/27-interphone-dome-photo-3-bottom-panel.jpg]
The printed bottom panel
<td align="center" width="50%"><br><sub>The bottom panel - the hole for the SERVICE INTERPHONE switch at the top, the recess for the top panel at the bottom</sub></td>
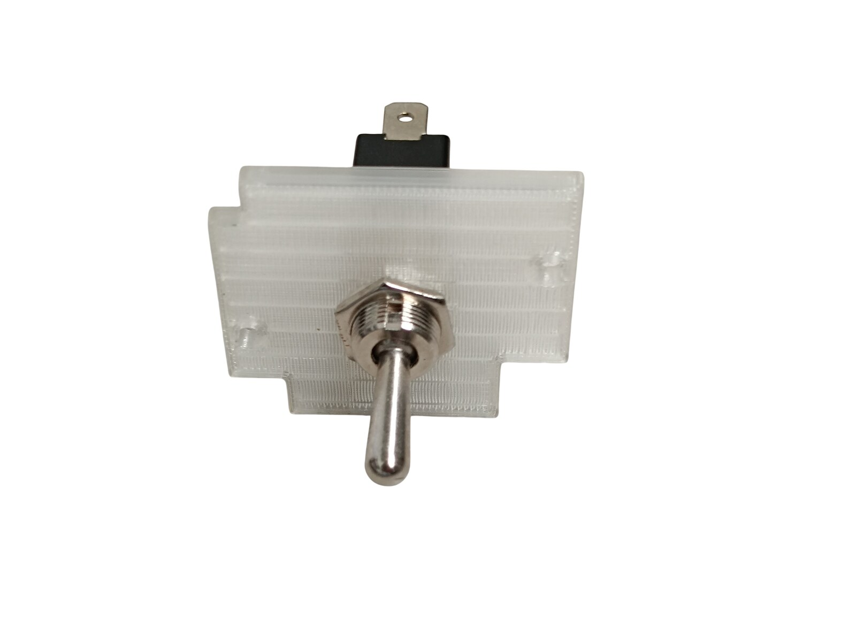
[picture p282: images/panels/27-interphone-dome-photo-4-diffuser.jpg]
Diffuser panel with the DOME WHITE switch fitted
<td align="center" width="50%"><br><sub>The diffuser panel with the DOME WHITE switch fitted</sub></td>
</tr>
</tbody>
<tbody>
<tr>
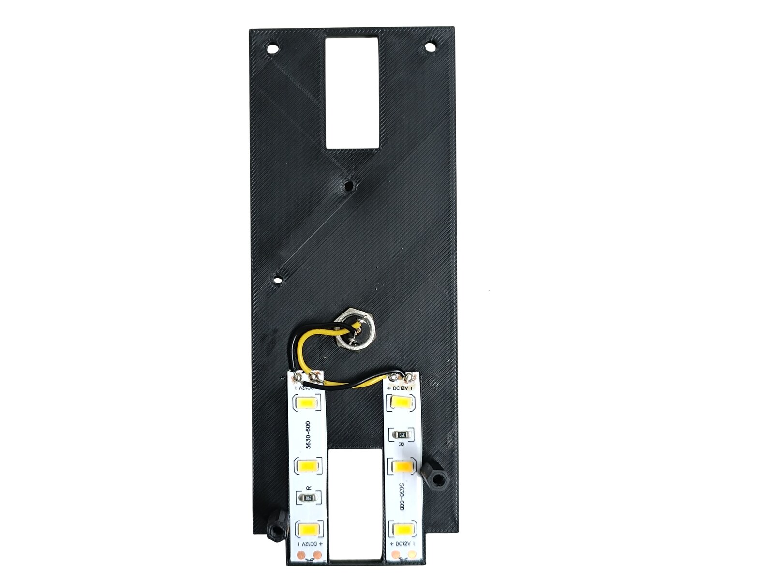
[picture p283: images/panels/27-interphone-dome-photo-5-backlight-panel.jpg]
Backlight panel with the LED strips and the DC jack
<td align="center" width="50%"><br><sub>The backlight panel with the two LED strips, the DC jack and the standoffs</sub></td>
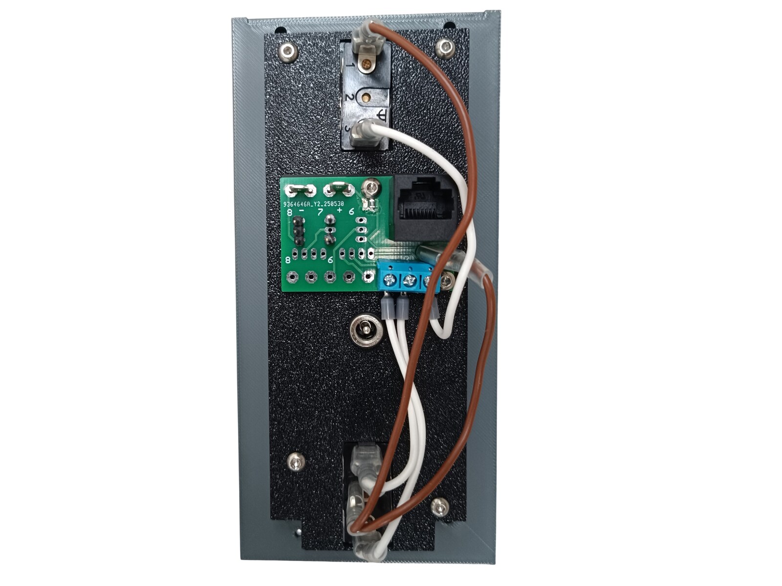
[picture p284: images/panels/27-interphone-dome-photo-6-rear.jpg]
Rear of the finished panel
<td align="center" width="50%"><br><sub>Rear side - the PCB, the two switches and the DC jack</sub></td>
</tr>
</tbody>
<tbody>
<tr>
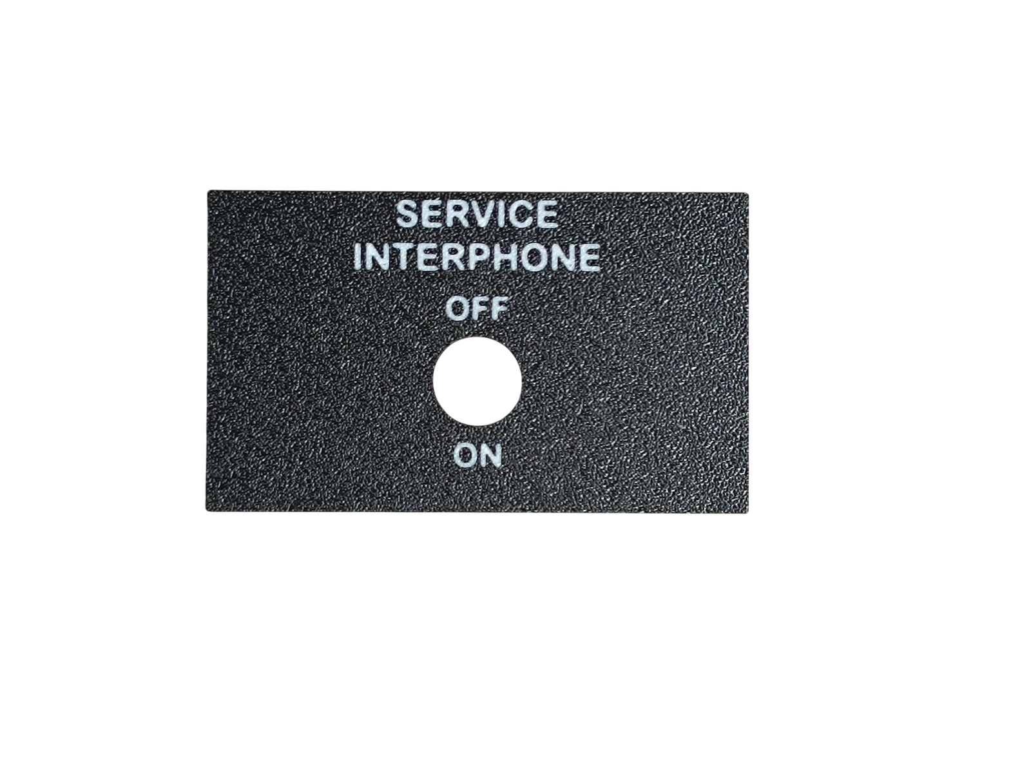
[picture p285: images/panels/27-interphone-dome-photo-7-plate.jpg]
The printed SERVICE INTERPHONE plate
<td align="center" width="50%"><br><sub>The plate - Black with the lettering in Jade White</sub></td>
<td align="center" width="50%"></td>
</tr>
</tbody>
</table>

---

## Filament

| | Colour | Filament |
|---|---|---|
|  | Dark Gray | C-Tech Premium Line PLA RAL7011 |
|  | Transparent | Filament PM PLA Transparent |
|  | White | Bambu PLA Basic Jade White (10100) |
|  | Black | Bambu PLA Basic Black (10101) |

---

## 3D Printed Parts

| Qty | Part | Notes |
|---:|---|---|
| 1× | Top panel | print on a **Textured** PEI plate |
| 1× | Bottom panel | print on a **Textured** PEI plate |
| 1× | Plate | print on a **Textured** PEI plate |
| 1× | Diffuser panel | print on a **Smooth** PEI plate |
| 1× | Backlight panel | |
| 1× | PCB frame | |
| 2× | Standoff 16 mm | |

---

## Switches and Buttons

| Qty | Type |
|---:|---|
| 1× | KN3(C)-101 or KN3(C)-102, ON/OFF |
| 1× | KN3(C)-103, ON/OFF/ON |

The two-position switch is SERVICE INTERPHONE, the three-position one is DOME WHITE - DIM, OFF and BRIGHT.

---

## Glue

The plate is glued onto the bottom panel.

> **Note**
> Do not use cyanoacrylate (superglue) here. As it cures it leaves a white film on the surface around the joint, not only where the glue was applied, and that shows on a black plate. A two-part epoxy is a good choice instead.

---

## Screws

| Qty | Screw | Joins |
|---:|---|---|
| 2× | Flat head M3×12 | bottom + standoff |
| 2× | Dome head M3×5 | PCB + backlight |
| 6× | Dome head M3×8 | top + bottom, backlight + standoff |
| 4× | Dome head M4×10 | bottom + main frame |

---

## PCB

| Qty | PCB | Connections used | Gerber files |
|---:|---|---|---|
| 1× | [RJ45 Direct](../pcb/rj45-direct.md) | pins 1–3 and 8 | [📥 PCB_RJ45_Direct.zip](https://raw.githubusercontent.com/om7ea/B737/main/PCB/PCB_RJ45_Direct.zip) |

Mounting is shown in [step 3](#3-backlight-panel---pcb-and-dc-jack) of the assembly diagram. Which switch each connection carries is in [Wiring](#wiring).

---

## Wiring

The panel takes **one** Ethernet patch cable to the [RJ45 Hub Shield](../pcb/rj45-hub-shield.md).

| PCB | Patch cable goes to | Connections used |
|---|---|---|
| **PCB 1** | socket **D1** on **Overhead_3** | pins 1–3 and 8 |

The socket labels **D0–D6**, **A1** and **A2** are silkscreened on the hub shield.

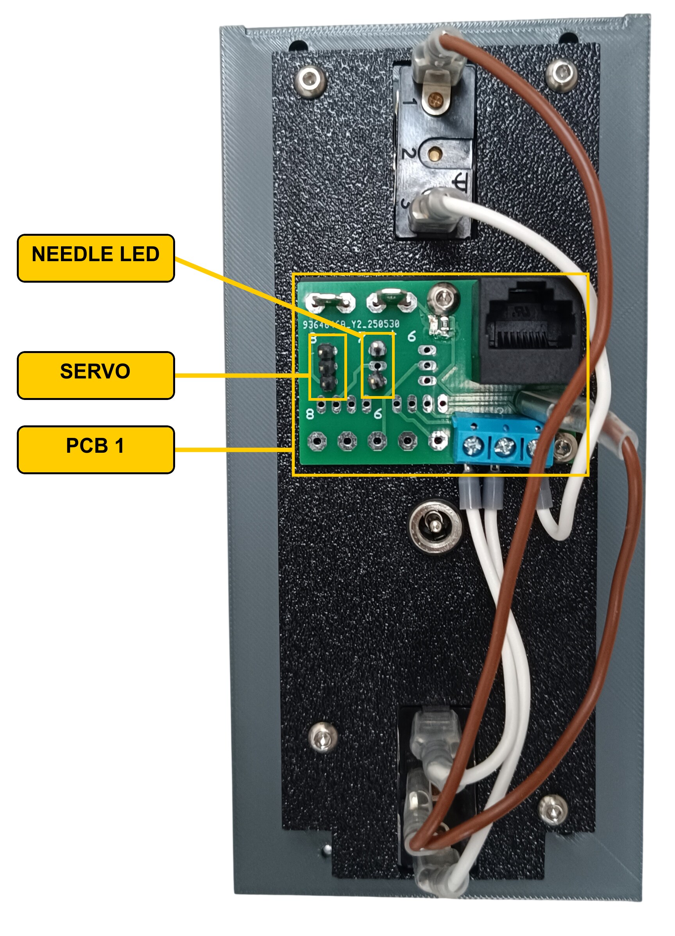
[picture p286: images/panels/27-interphone-dome-wiring-rear.jpg]
Rear of the panel with the PCB and the two pin header groups marked


The rear of the panel. The board carries a three-way blue screw terminal at the pin 1 end; the brown wire runs up to the SERVICE INTERPHONE switch, the two white ones down to DOME WHITE. Both marked groups of pin headers belong to the Crew oxygen pressure gauge - all three pins at position **8** for the servo, and the outer two at position **7**, the **-** and the **+**, for the needle LED. The middle pin at position 7 stays free.

### PCB 1 - socket D1 on Overhead_3

| Pin | Switch |
|---:|---|
| 1 | SERVICE INTERPHONE |
| 2 | DOME WHITE - BRIGHT |
| 3 | DOME WHITE - DIM |
| 8 | Crew oxygen pressure gauge - servo signal |

Pin 8 does not belong to this panel. It drives the servo of the [Crew oxygen pressure gauge](29-oxygen-pressure-gauge.md) on the **[Engine and Oxygen Panel](30-engine-and-oxygen-panel.md)**: the PCBs on that panel are fully taken, so I feed the gauge from this board instead. The servo takes three of the pin headers at the pin 8 position - the signal, **GND** and **+5 V** - and its plug has to be rewired before it will work, see [Oxygen Pressure Gauge](29-oxygen-pressure-gauge.md#wiring).

That gauge's **needle LED** is fed from this board as well: its **+5 V** and **GND** come from the pin headers too.

**Both switches share a single ground return.** Each switch takes one of its terminals to its own pin on the Direct PCB. The opposite terminals are commoned - daisy-chained from one switch to the next - and the chain ends at a **-** (ground) contact.

---

## Backlight

| Qty | Part | Reference |
|---:|---|---|
| 2× | LED strip | [Product I used](../../images/parts/AE_led_strip.png) |
| 1× | DC jack 5.5 × 2.5 mm | [Product I used](../../images/parts/AE_dc_jack.png) |

Powered from the **12 V** supply - see [Power supply](../system-overview.md#power-supply).

---

## Assembly Diagram

Screw abbreviations used in the diagrams: **FH** = flat head, **DH** = dome head.

### 1. Bottom panel - diffuser, switches and standoffs

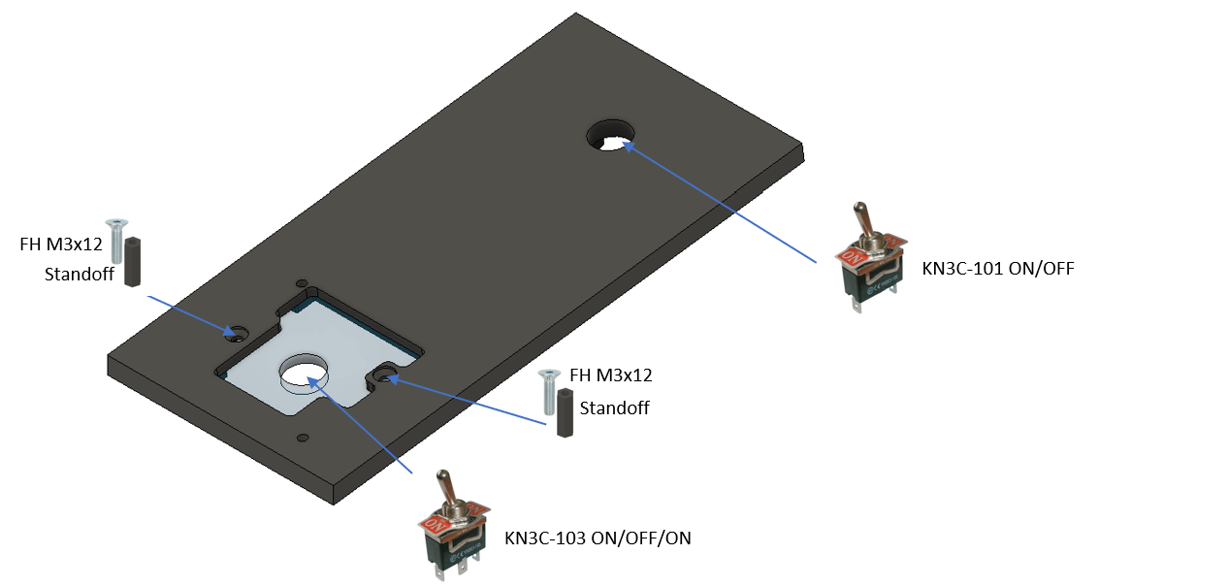
[picture p287: images/panels/27-interphone-dome-01-bottom-panel.png]
Bottom panel with the diffuser, the two switches and the standoffs


### 2. Backlight panel - LED strips

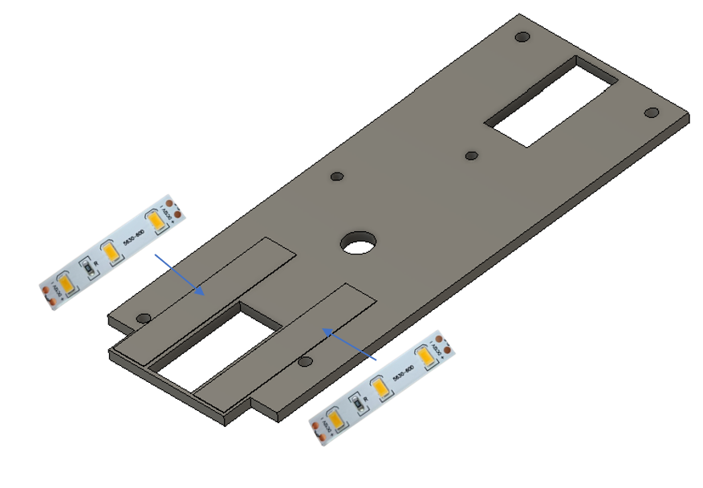
[picture p288: images/panels/27-interphone-dome-02-backlight-leds.png]
The two backlight LED strips


### 3. Backlight panel - PCB and DC jack

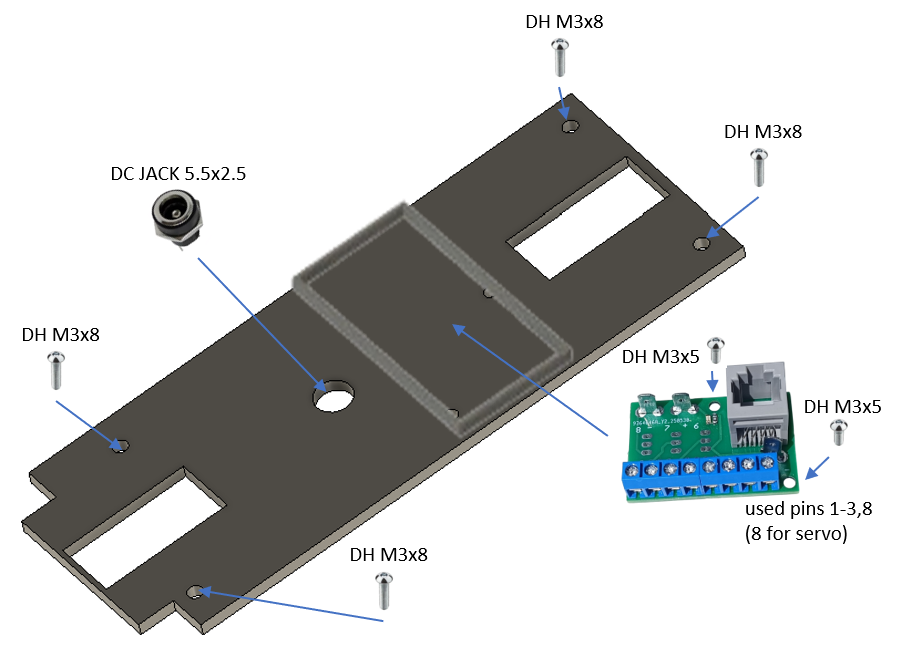
[picture p289: images/panels/27-interphone-dome-03-pcb-and-dc-jack.png]
Backlight panel with the PCB and the DC jack


### 4. Top panel

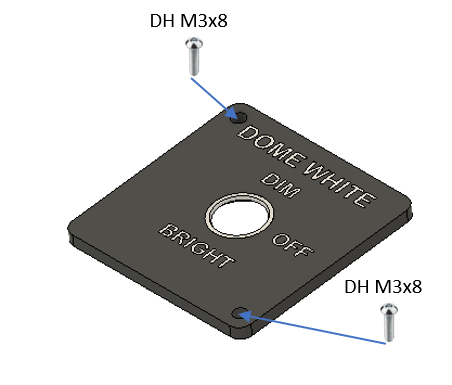
[picture p290: images/panels/27-interphone-dome-04-top-panel.png]
Top panel screwed into the recess of the bottom panel


### 5. Panel on the main frame

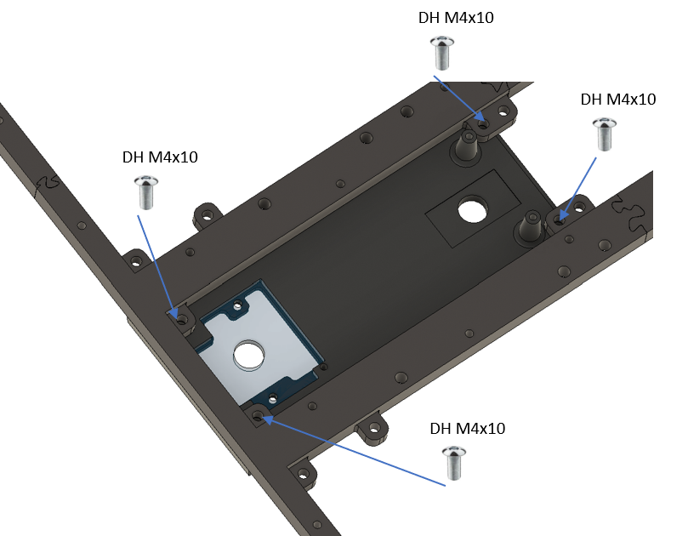
[picture p291: images/panels/27-interphone-dome-05-main-frame.png]
The finished panel screwed to the main frame
