om7ea/B737/docs/models/22-fuel-control-panel.md

# 22. Fuel Control Panel

[📦 Download the printable model on MakerWorld](https://makerworld.com/en/models/3260961-boeing-737-overhead-fuel-control-panel)

[← Back to model list](README.md)

---

## Photos

<table>
<tbody>
<tr>
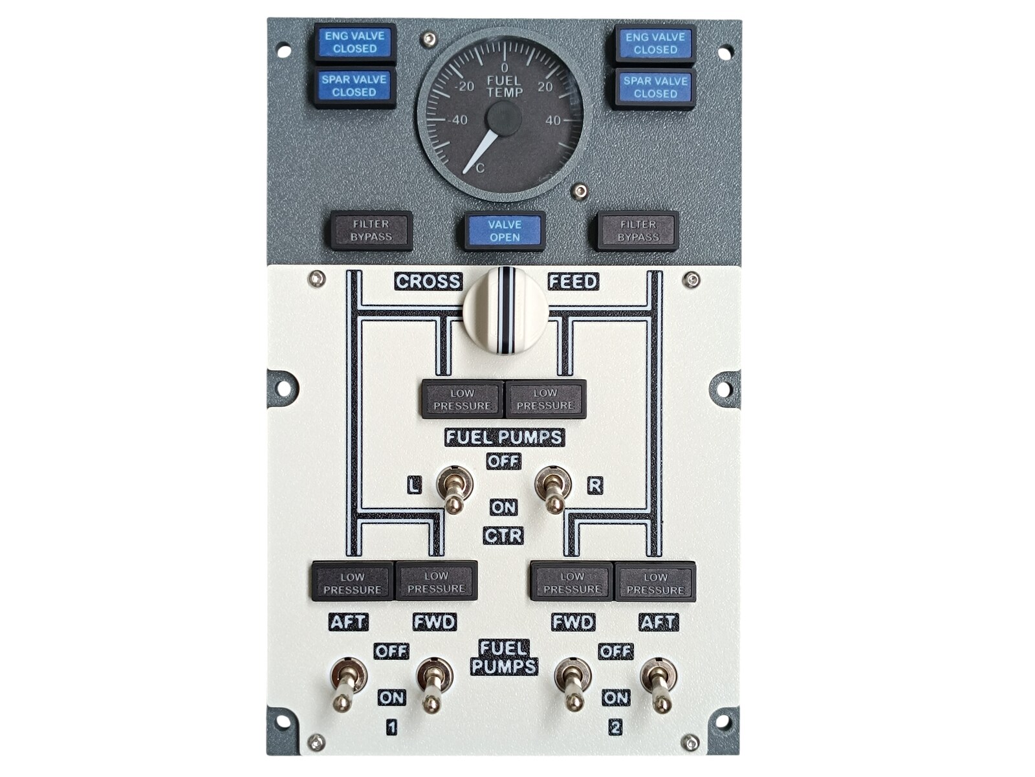
[picture p304: images/panels/22-fuel-control-photo-1-front.jpg]
Finished Fuel Control Panel, front
<td align="center" width="50%"><br><sub>Finished panel</sub></td>
<td align="center" width="50%">Printed top panel<br><sub>Top panel - Bone White, with the lettering and the lines in Black and Jade White</sub></td>
</tr>
</tbody>
<tbody>
<tr>
<td align="center" width="50%">Bottom panel with the annunciators, the gauge and the diffuser fitted<br><sub>The annunciators, the gauge and the diffuser with the switches, before the top panel goes on</sub></td>
<td align="center" width="50%">Rear of the finished panel<br><sub>Rear side - the four PCBs, the gauge and the DC jack</sub></td>
</tr>
</tbody>
</table>

---

## Filament

| | Colour | Filament |
|---|---|---|
|  | Dark Gray | C-Tech Premium Line PLA RAL7011 |
|  | Bone White | Bambu PLA Matte Bone White (11103) |
|  | Transparent | Filament PM PLA Transparent |
|  | White | Bambu PLA Basic Jade White (10100) |
|  | Black | Bambu PLA Basic Black (10101) |

---

## 3D Printed Parts

| Qty | Part | Notes |
|---:|---|---|
| 1× | Top panel | print on a **Textured** PEI plate |
| 1× | Bottom panel | print on a **Textured** PEI plate |
| 1× | Diffuser panel | print on a **Smooth** PEI plate |
| 1× | Backlight panel | |
| 1× | Bezel | the ring around the gauge window |
| 4× | PCB frame | |
| 6× | M4 washer | |
| 4× | Standoff 16 mm | |

---

## Switches and Buttons

| Qty | Type |
|---:|---|
| 6× | KN3(C)-101 or KN3(C)-102, ON/OFF |
| 1× | Rotary switch SR16, 8 positions |

The six toggle switches are the FUEL PUMPS switches, the rotary switch is CROSS FEED.

> **Note**
> With the knob already fitted, I turned the CROSS FEED selector hard against its end stop until the stop broke off inside the switch. What is left is a switch that turns continuously in both directions instead of running out of travel. I used the same trick on the [AC and DC Meter Panel](26-ac-and-dc-meter-panel.md).

---

## Rotary Knobs

The knob for the CROSS FEED selector is a separate model shared with the other panels - it is **not included** in this download.

| Qty | Part |
|---:|---|
| 1× | Fuel cross feed knob |
| 1× | Fuel cross feed knob indicator |

| | |
|---|---|
| 📦 Printable model | [Boeing 737 Overhead - Rotary Knobs](https://makerworld.com/en/models/3066127-boeing-737-overhead-rotary-knobs) |
| 🔧 Build notes | [Rotary Knobs](03-rotary-knobs.md) |

---

## Gauge

The FUEL TEMP instrument is a separate model shared with three other panels - it is **not included** in this download. The bezel that rings it is part of this panel; the acrylic window between the two is not printed at all, it is cut - see [CNC Cut Files](#cnc-cut-files).

| | |
|---|---|
| 📦 Printable model | [Boeing 737 Overhead - Temperature and Climb Gauges](https://makerworld.com/en/models/3251829-boeing-737-overhead-temperature-and-climb-gauges) |
| 🔧 Build notes | [Temperature and Climb Gauges](21-temperature-and-climb-gauges.md) |

The needle to fit is **hand-fuel_white + hand-fuel_black**, and the scale is the FUEL TEMP dial on the [UV print sheet](../uv-print.md). Its three connections are in [Wiring](#wiring).

---

## Screws

| Qty | Screw | Joins |
|---:|---|---|
| 1× | Flat head M3×6 | bottom + diffuser |
| 4× | Flat head M3×12 | bottom + standoff |
| 6× | Flat head M4×16 | bottom + main frame |
| 8× | Dome head M3×5 | PCB + backlight |
| 8× | Dome head M3×8 | top + bottom, backlight + standoff |
| 2× | Dome head M3×12 | bottom + gauge |

The six M4×16 screws each take one of the printed M4 washers.

---

## Annunciators

| Qty | Type |
|---:|---|
| 8× | Black background, yellow LED |
| 5× | Blue background, white LED, two brightness levels (DIM/BRIGHT) |

The yellow ones are the six LOW PRESSURE and the two FILTER BYPASS annunciators. The blue ones are ENG VALVE CLOSED and SPAR VALVE CLOSED, twice each, and VALVE OPEN.

The annunciators are a separate model shared with the other panels - they are **not included** in this download.

| | |
|---|---|
| 📦 Printable model | [Boeing 737 Overhead - Annunciators](https://makerworld.com/en/models/3121595-boeing-737-overhead-annunciators) |
| 🔧 Build notes | [Annunciators](02-annunciators.md) |
| 🔌 PCB, BOM and wiring | [Annunciator PCB](../pcb/annunciator.md) |

---

## CNC Cut Files

| Qty | File | Size |
|---:|---|---|
| 1× | cnc_gauge_48-8.dxf | Ø 48.8 mm |

This is the round window that goes in front of the FUEL TEMP gauge, behind the bezel. The drawing, the material and the cutting notes are on the [CNC Cut Files](../cnc-cut.md) page.

The window is glued to the bezel.

> **Note**
> Do not use cyanoacrylate (superglue) for that joint. As it cures it leaves a white film on the surface around the joint, not only where the glue was applied, and on a clear window it is impossible to miss. A two-part epoxy is a good choice instead.

---

## PCB

| Qty | PCB | Connections used | Gerber files |
|---:|---|---|---|
| 3× | [RJ45 LED Driver](../pcb/rj45-driver.md) | headers 1–8 on two of them, 3–4 on the third | [📥 PCB_RJ45_Driver.zip](https://raw.githubusercontent.com/om7ea/B737/main/PCB/PCB_RJ45_Driver.zip) |
| 1× | [RJ45 Direct](../pcb/rj45-direct.md) | pins 1–8 | [📥 PCB_RJ45_Direct.zip](https://raw.githubusercontent.com/om7ea/B737/main/PCB/PCB_RJ45_Direct.zip) |

Mounting is shown in [step 3](#3-backlight-panel---pcbs-and-dc-jack) of the assembly diagram. Which switch and which annunciator each connection carries is in [Wiring](#wiring).

---

## Wiring

Everything on this panel reaches the same MEGA 2560 - `Overhead_1b`. The panel takes **four** Ethernet patch cables to the [RJ45 Hub Shield](../pcb/rj45-hub-shield.md).

| PCB | Patch cable goes to | Connections used |
|---|---|---|
| **PCB 1** | socket **D0** on **Overhead_1b** | headers 1–8 |
| **PCB 2** | socket **D1** on **Overhead_1b** | headers 3–4 |
| **PCB 3** | socket **D2** on **Overhead_1b** | headers 1–8 |
| **PCB 4** | socket **D3** on **Overhead_1b** | pins 1–8 |

The socket labels **D0–D6**, **A1** and **A2** are silkscreened on the hub shield.

Rear of the panel with the four PCBs marked

The rear of the panel. **PCB 1** and **PCB 3** are the two boards side by side under the gauge, each one wired to the annunciators of the half of the panel it sits on. **PCB 2** is below them, mounted on its side, with only two of its headers populated. **PCB 4** is the board with the blue eight-way screw terminal; the black pin header beside it is where the servo plugs in.

### PCB 1 - socket D0 on Overhead_1b

| Header | Annunciator |
|---:|---|
| 1 | ENG VALVE CLOSED - right, bright |
| 2 | SPAR VALVE CLOSED - right, dim |
| 3 | VALVE OPEN - bright |
| 4 | FILTER BYPASS - right |
| 5 | LOW PRESSURE - CTR R |
| 6 | VALVE OPEN - dim |
| 7 | SPAR VALVE CLOSED - right, bright |
| 8 | ENG VALVE CLOSED - right, dim |

### PCB 2 - socket D1 on Overhead_1b

| Header | Annunciator |
|---:|---|
| 3 | LOW PRESSURE - 2 AFT |
| 4 | LOW PRESSURE - 2 FWD |

Headers 1, 2 and 5 to 8 are not populated.

### PCB 3 - socket D2 on Overhead_1b

| Header | Annunciator |
|---:|---|
| 1 | ENG VALVE CLOSED - left, bright |
| 2 | SPAR VALVE CLOSED - left, bright |
| 3 | FILTER BYPASS - left |
| 4 | LOW PRESSURE - 1 FWD |
| 5 | LOW PRESSURE - 1 AFT |
| 6 | LOW PRESSURE - CTR L |
| 7 | SPAR VALVE CLOSED - left, dim |
| 8 | ENG VALVE CLOSED - left, dim |

All six LOW PRESSURE annunciators carry the same printed text. Each one sits directly above the pump switch it belongs to, and the qualifier in the tables is the marking beside that switch: **CTR L** and **CTR R** for the centre tank pumps, **1 FWD**, **1 AFT**, **2 FWD** and **2 AFT** for the four below.

> **Note**
> All five blue annunciators are the dual brightness type and all five are **wired** for it: each has a second connector that feeds the LED without the 150 Ω resistor - see [Annunciator PCB](../pcb/annunciator.md). Only VALVE OPEN is driven at both levels; the four **bright** rows above have no configuration in the [MobiFlight project](../mobiflight.md), so those four lamps light dim only. I did not find a way to read the second brightness level out of the PMDG 737-800 - the wiring is there, so anyone who finds it only has to add the configuration.

### PCB 4 - socket D3 on Overhead_1b

| Pin | Switch |
|---:|---|
| 1 | FUEL PUMPS - 1 AFT |
| 2 | FUEL PUMPS - 1 FWD |
| 3 | FUEL PUMPS - 2 FWD |
| 4 | FUEL PUMPS - 2 AFT |
| 5 | FUEL PUMPS - CTR R |
| 6 | CROSS FEED |
| 7 | FUEL PUMPS - CTR L |
| 8 | FUEL TEMP gauge - servo signal |

Pins 1 to 4 follow the four lower switches left to right as they appear on the front of the panel.

The CROSS FEED selector is wired as a two-position switch, and it takes **two** contacts of the SR16 - the two that face each other. Both go to pin 6, so the selector stays closed when the knob is turned on through 180°, the way the bar-shaped knob suggests it should.

The gauge takes two more connections from this board that are not on the screw terminal: the servo's **+5 V** and **GND**, and the **+5 V** and **GND** of the needle LED, all from the pin headers. Its scale backlight runs on 12 V from this panel's own backlighting, through the lever-type splice connector above the gauge. The servo plug has to be rewired before it will work - see [Temperature and Climb Gauges](21-temperature-and-climb-gauges.md#wiring).

**All the switches share a single ground return.** Each switch takes one of its terminals to its own pin on the Direct PCB. The opposite terminals are commoned - daisy-chained from one switch to the next - and the chain ends at a **-** (ground) contact.

---

## Backlight

| Qty | Part | Reference |
|---:|---|---|
| 8× | LED strip | [Product I used](../../images/parts/AE_led_strip.png) |
| 1× | DC jack 5.5 × 2.5 mm | [Product I used](../../images/parts/AE_dc_jack.png) |

Powered from the **12 V** supply - see [Power supply](../system-overview.md#power-supply).

---

## Assembly Diagram

Screw abbreviations used in the diagrams: **FH** = flat head, **DH** = dome head.

### 1. Bottom panel - diffuser, annunciators, gauge and switches

Bottom panel with the diffuser, annunciators, gauge, switches and standoffs

The six M4×16 screws in this drawing are the ones that later hold the finished panel on the main frame.

### 2. Backlight panel - LED strips

The eight backlight LED strips

### 3. Backlight panel - PCBs and DC jack

Backlight panel with the four PCBs and the DC jack

### 4. Top panel

Top panel screwed to the bottom panel
