om7ea/B737/docs/models/25-pressurization-altitude-info.md

# 25. Pressurization Altitude Info

[📦 Download the printable model on MakerWorld](https://makerworld.com/en/models/3287240-boeing-737-overhead-pressurization-altitude-info)

[← Back to model list](README.md)

---

## Photos

<table>
<tbody>
<tr>
<td align="center" width="50%">Finished Pressurization Altitude Info plate, front<br><sub>Finished plate</sub></td>
<td align="center" width="50%">Printed bottom panel with the two M4 washers<br><sub>The bottom panel and the two printed M4 washers</sub></td>
</tr>
</tbody>
<tbody>
<tr>
<td align="center" width="50%">The printed info plate<br><sub>The info plate - Black with the lettering in Jade White</sub></td>
<td align="center" width="50%"></td>
</tr>
</tbody>
</table>

---

## Filament

| | Colour | Filament |
|---|---|---|
|  | Dark Gray | C-Tech Premium Line PLA RAL7011 |
|  | White | Bambu PLA Basic Jade White (10100) |
|  | Black | Bambu PLA Basic Black (10101) |

---

## 3D Printed Parts

| Qty | Part | Notes |
|---:|---|---|
| 1× | Bottom panel | print on a **Textured** PEI plate |
| 1× | Info plate | the Black plate with the Jade White lettering; print on a **Textured** PEI plate |
| 2× | M4 washer | |

---

## Glue

The info plate is glued onto the bottom panel. It is exactly as tall as the panel, so the top and bottom edges line up by themselves and the only thing to get right is the sideways position - leave the same amount of the bottom panel showing at each end.

> **Note**
> Do not use cyanoacrylate (superglue) here. As it cures it leaves a white film on the surface around the joint, not only where the glue was applied, and that shows on a black plate. A two-part epoxy is a good choice instead.

---

## Screws

| Qty | Screw | Joins |
|---:|---|---|
| 2× | Flat head M4×16 | bottom + main frame |

The two M4×16 screws each take one of the printed M4 washers.

---

## Assembly Diagram

Screw abbreviations used in the diagram: **FH** = flat head.

### 1. Info plate and mounting to the main frame

Info plate glued into the bottom panel and the panel screwed to the main frame
