om7ea/B737/docs/models/12-voice-recorder-switch.md

# 12. Voice Recorder Switch

[📦 Download the printable model on MakerWorld](https://makerworld.com/en/models/3214222-boeing-737-overhead-voice-recorder-switch)

[← Back to model list](README.md)

---

## Photos

<table>
<tbody>
<tr>
<td align="center" width="50%">Finished Voice Recorder Switch, front<br><sub>Finished panel</sub></td>
<td align="center" width="50%">Printed top panel<br><sub>Printed top panel</sub></td>
</tr>
</tbody>
<tbody>
<tr>
<td align="center" width="50%">Printed bottom panel<br><sub>Printed bottom panel</sub></td>
<td align="center" width="50%">Diffuser panel with the switch fitted<br><sub>Diffuser panel with the switch fitted</sub></td>
</tr>
</tbody>
<tbody>
<tr>
<td align="center" width="50%">Diffuser panel fitted into the bottom panel<br><sub>Diffuser panel fitted, before the top panel goes on</sub></td>
<td align="center" width="50%">Inside of the backlight panel with the LED strip<br><sub>Backlight panel from the inside - LED strip and DC jack wiring</sub></td>
</tr>
</tbody>
<tbody>
<tr>
<td align="center" width="50%">Outside of the backlight panel with the DC jack<br><sub>Backlight panel from the outside - DC jack</sub></td>
<td align="center" width="50%">Rear of the assembled panel<br><sub>Rear side - backlight panel mounted, switch terminals and DC jack</sub></td>
</tr>
</tbody>
</table>

---

## Filament

| | Colour | Filament |
|---|---|---|
|  | Dark Gray | C-Tech Premium Line PLA RAL7011 |
|  | Transparent | Filament PM PLA Transparent |
|  | White | Bambu PLA Basic Jade White (10100) |
|  | Black | Bambu PLA Basic Black (10101) |

---

## 3D Printed Parts

| Qty | Part | Notes |
|---:|---|---|
| 1× | Top panel | print on a **Textured** PEI plate |
| 1× | Bottom panel | print on a **Textured** PEI plate |
| 1× | Diffuser panel | print on a **Smooth** PEI plate |
| 1× | Backlight panel | |
| 2× | M4 washer | |
| 4× | Standoff 16 mm | |

---

## Switches and Buttons

| Qty | Type |
|---:|---|
| 1× | KN3(C)-101 or KN3(C)-102, ON/OFF |

---

## Screws

| Qty | Screw | Joins |
|---:|---|---|
| 1× | Flat head M3×6 | bottom + diffuser |
| 4× | Flat head M3×12 | bottom + standoff |
| 2× | Flat head M4×16 | bottom + main frame |
| 6× | Dome head M3×8 | top + bottom, backlight + standoff |

---

## Wiring

This panel has no PCB and no patch cable of its own. Its single switch is wired across to a PCB on the [Air Conditioning Control Panel](24-air-conditioning-control-panel.md), where it takes pin **5** - that PCB's cable goes to socket **A2** on **Overhead_5**.

**Both wires come from that panel**, the signal and the ground return, so nothing here connects to a MEGA 2560 directly.

---

## Backlight

| Qty | Part | Reference |
|---:|---|---|
| 1× | LED strip | [Product I used](../../images/parts/AE_led_strip.png) |
| 1× | DC jack 5.5 × 2.5 mm | [Product I used](../../images/parts/AE_dc_jack.png) |

Powered from the **12 V** supply - see [Power supply](../system-overview.md#power-supply).

---

## Assembly Diagram

Screw abbreviations used in the diagrams: **FH** = flat head, **DH** = dome head.

### 1. Top panel

Top panel assembly

### 2. Bottom panel - diffuser, switch and standoffs

Bottom panel assembly

### 3. Backlight panel - LED strip

Backlight LED strip

### 4. Backlight panel - DC jack

Backlight panel DC jack mounting
