om7ea/B737/images/parts/AE_6digit_display.png

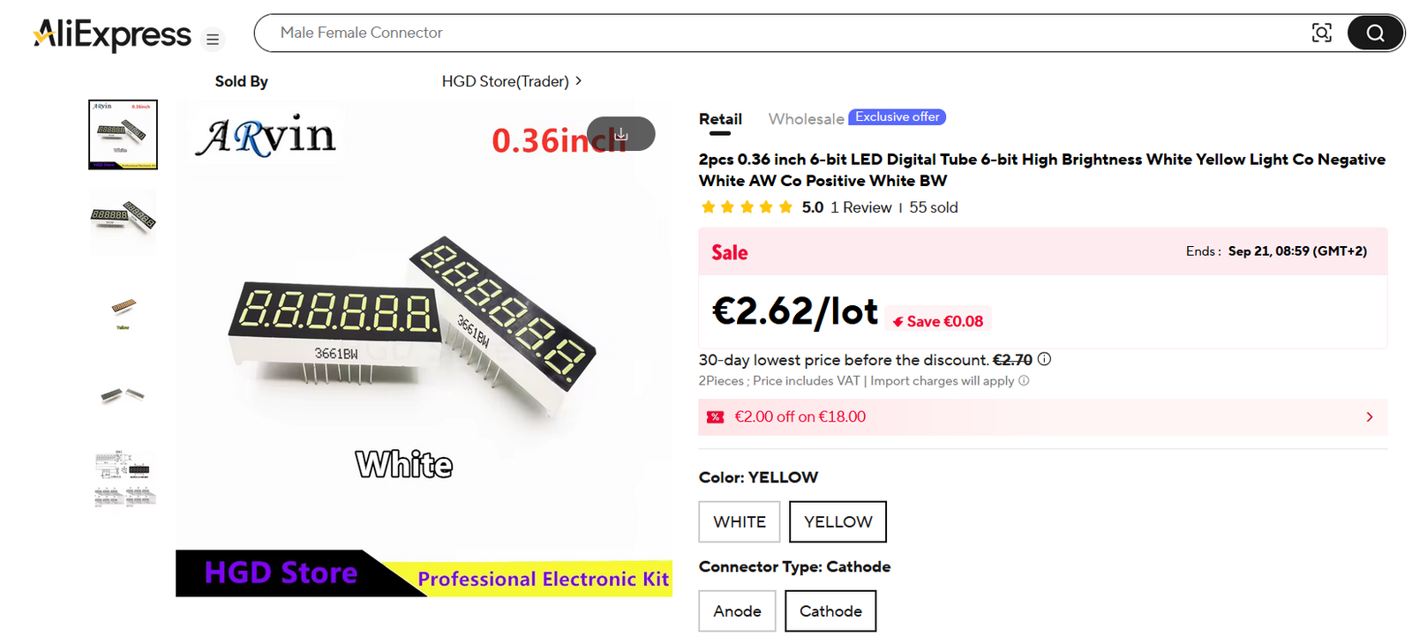
images/parts/AE_6digit_display.png
