om7ea/B737/images/parts/AE_7seg_display.png

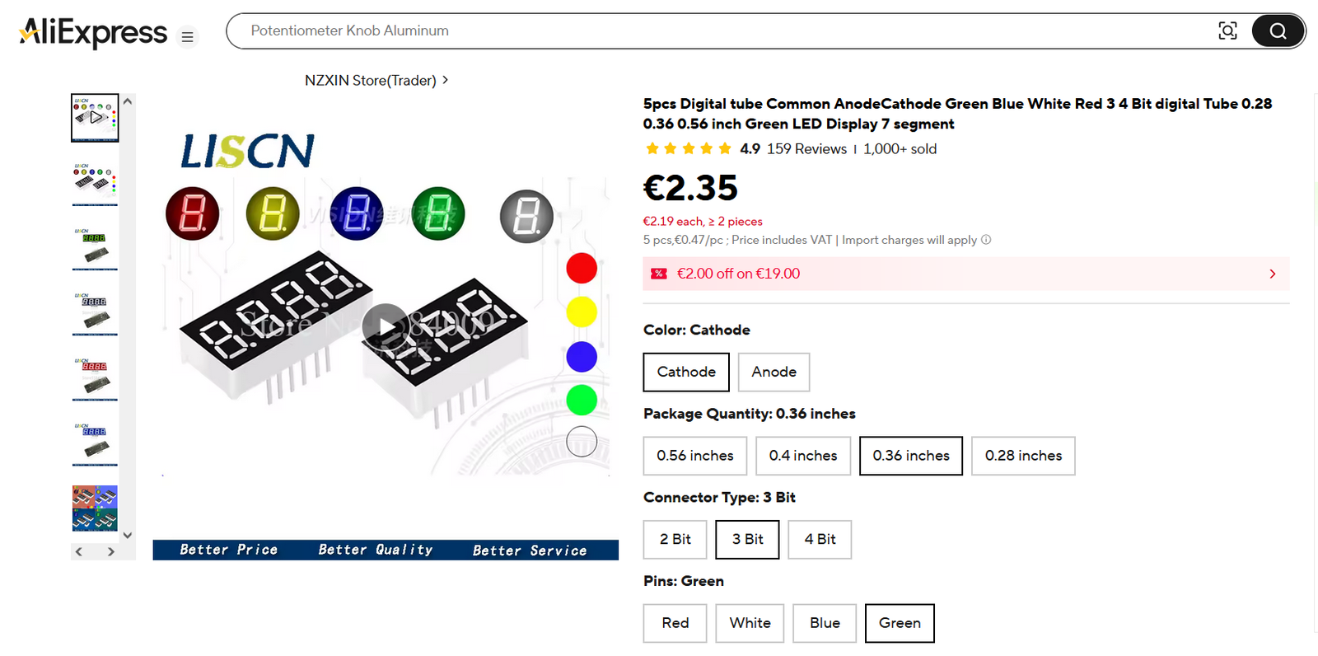
images/parts/AE_7seg_display.png
