om7ea/B737/images/parts/AE_acrylic_rod.png

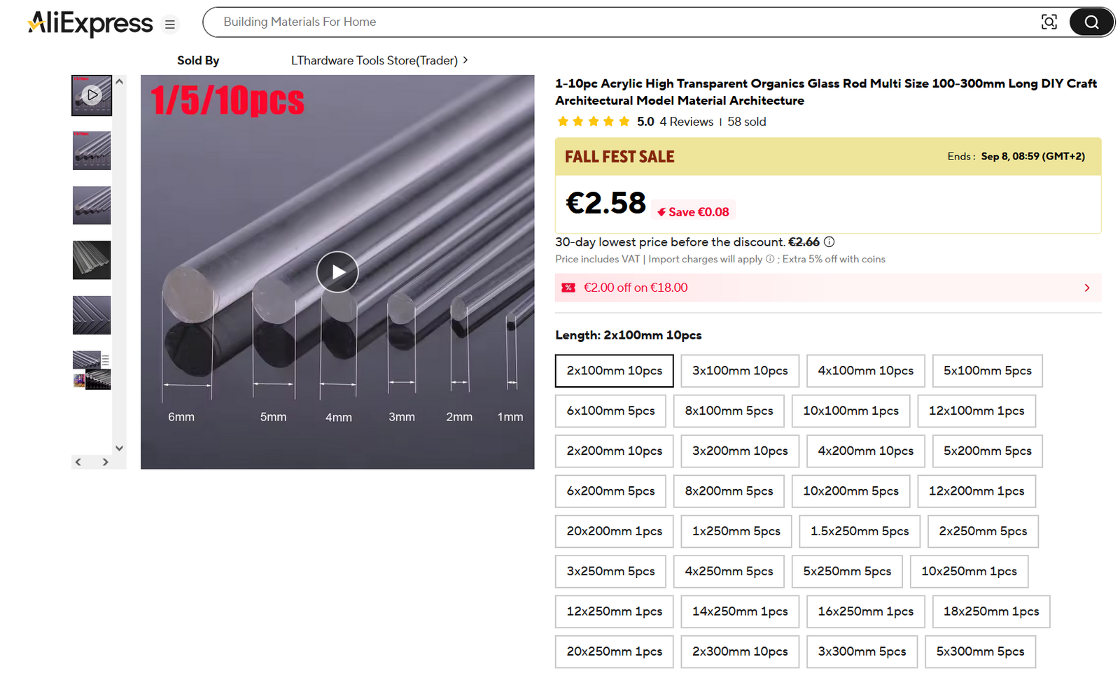
images/parts/AE_acrylic_rod.png
