om7ea/B737/images/parts/AE_bearing_MR63ZZ.png

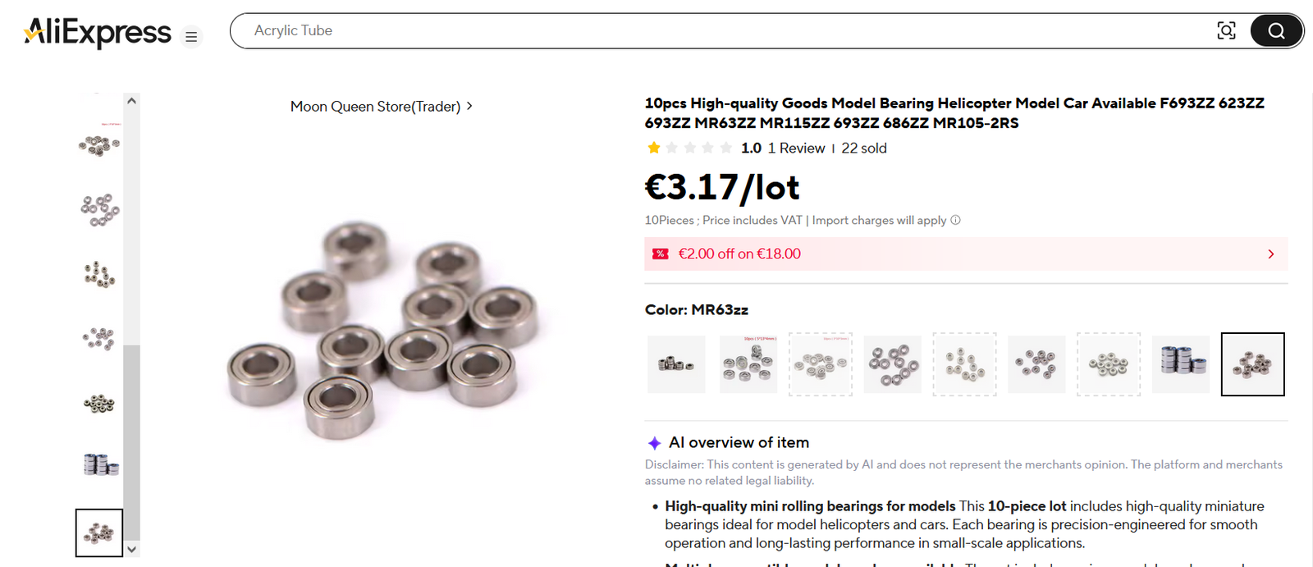
images/parts/AE_bearing_MR63ZZ.png
