om7ea/B737/images/parts/AE_button.png

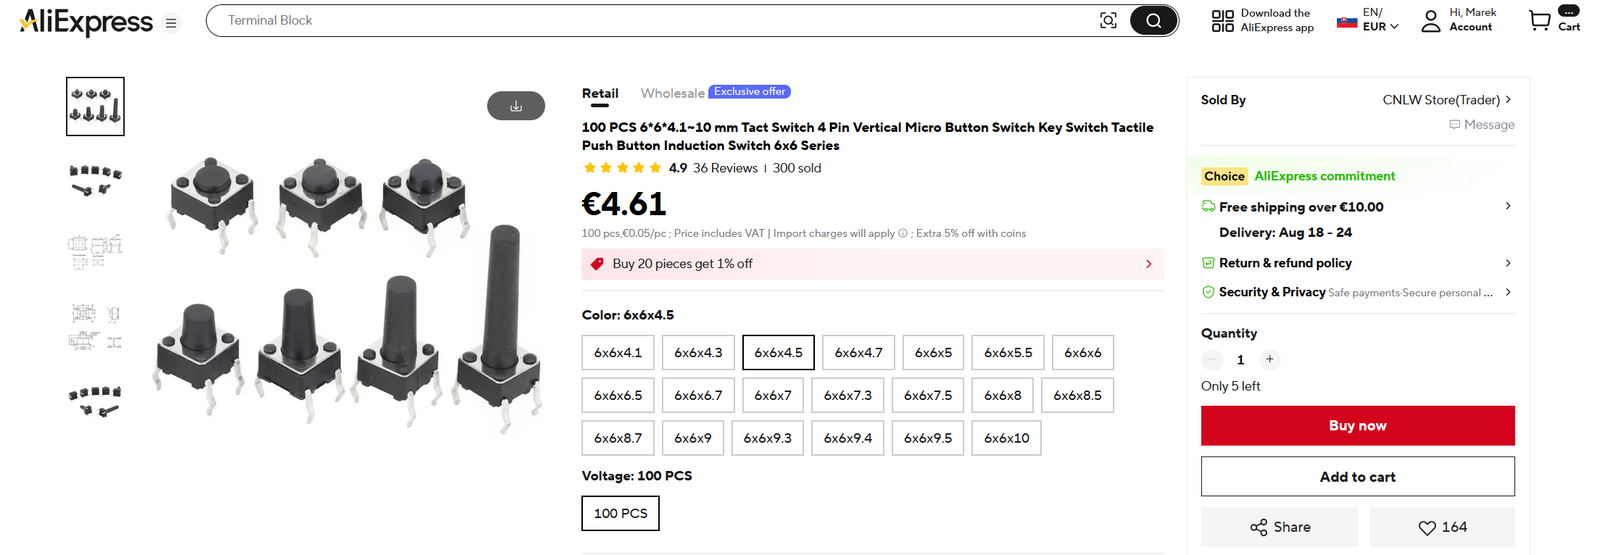
images/parts/AE_button.png
