om7ea/B737/images/parts/AE_button_led.png

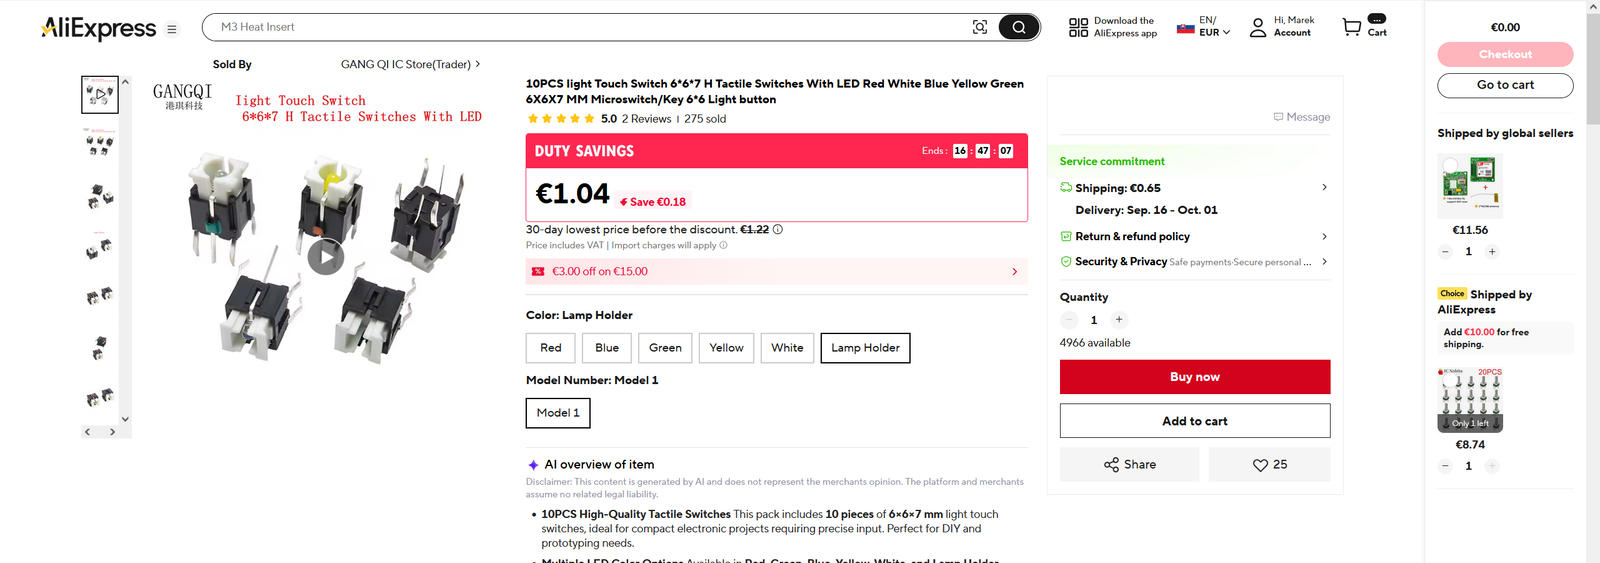
images/parts/AE_button_led.png
