om7ea/B737/images/parts/AE_dc_jack.png

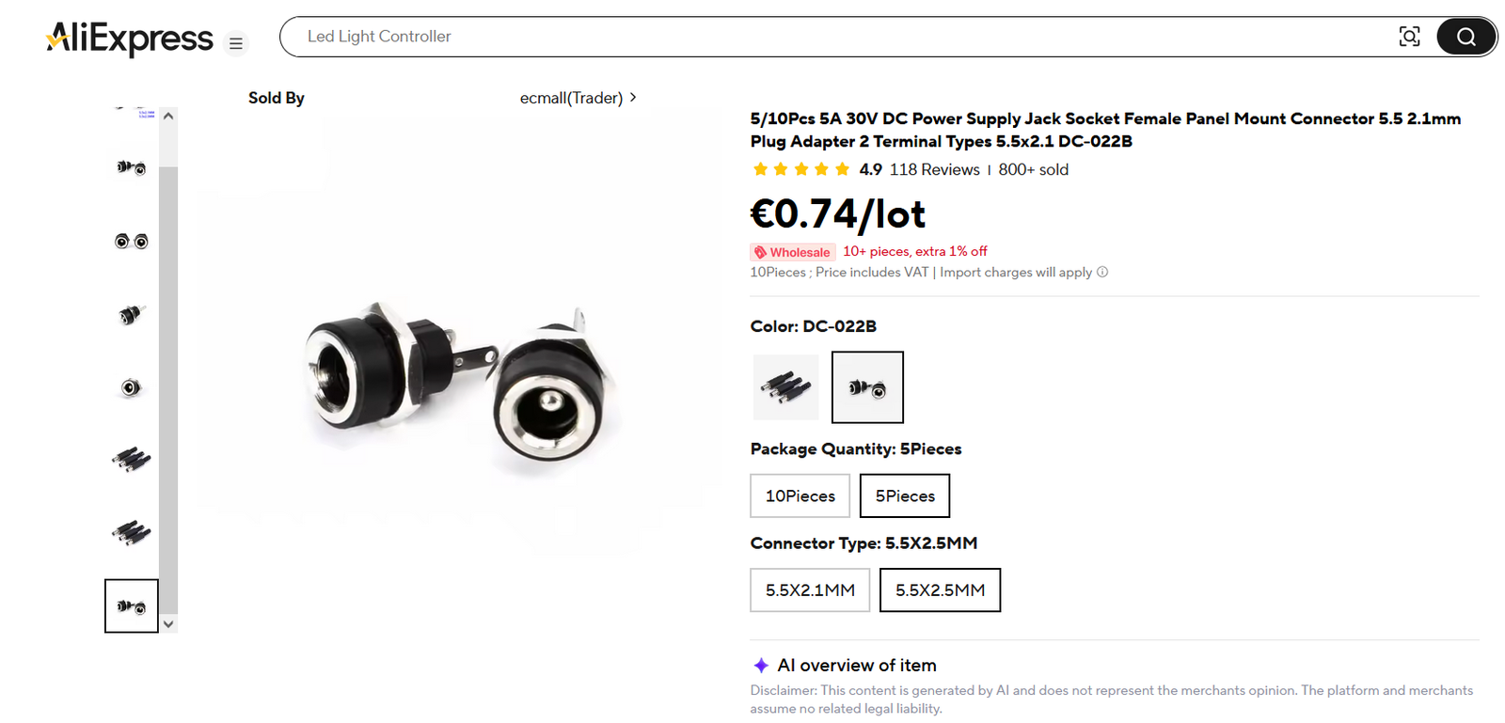
images/parts/AE_dc_jack.png
