om7ea/B737/images/parts/AE_dimmer.png

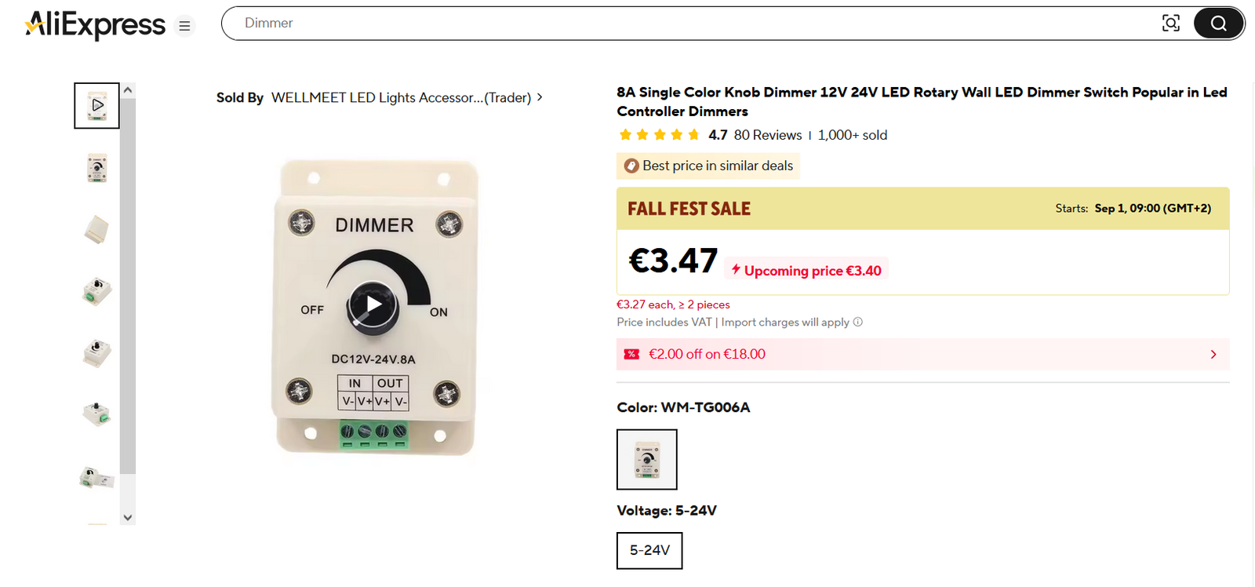
images/parts/AE_dimmer.png
