om7ea/B737/images/parts/AE_dupont_3p.png

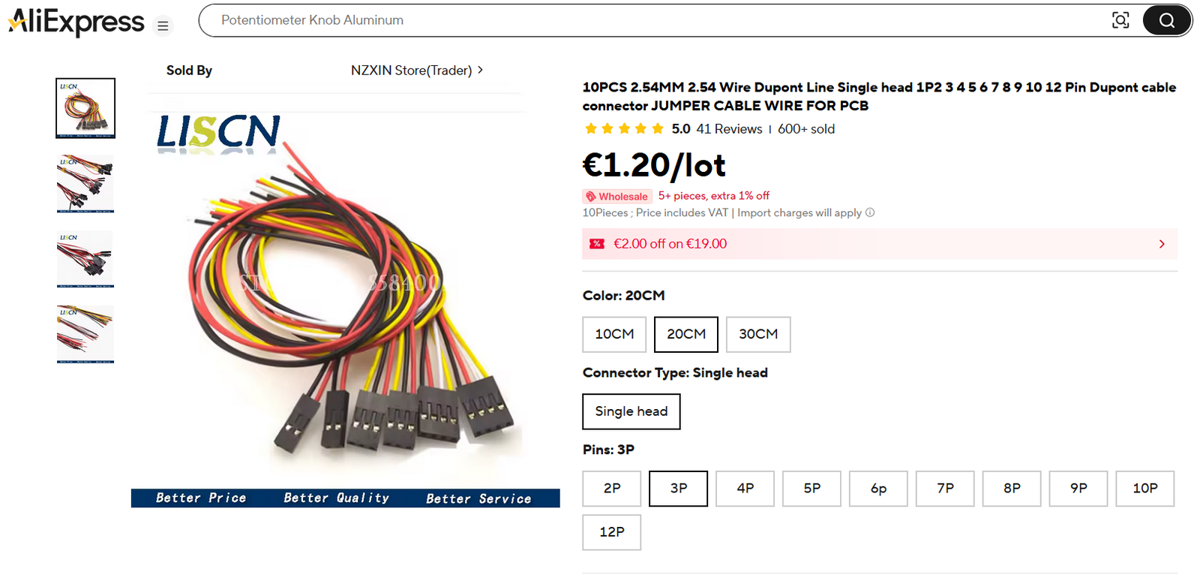
images/parts/AE_dupont_3p.png
