om7ea/B737/images/parts/AE_dupont_5p.png

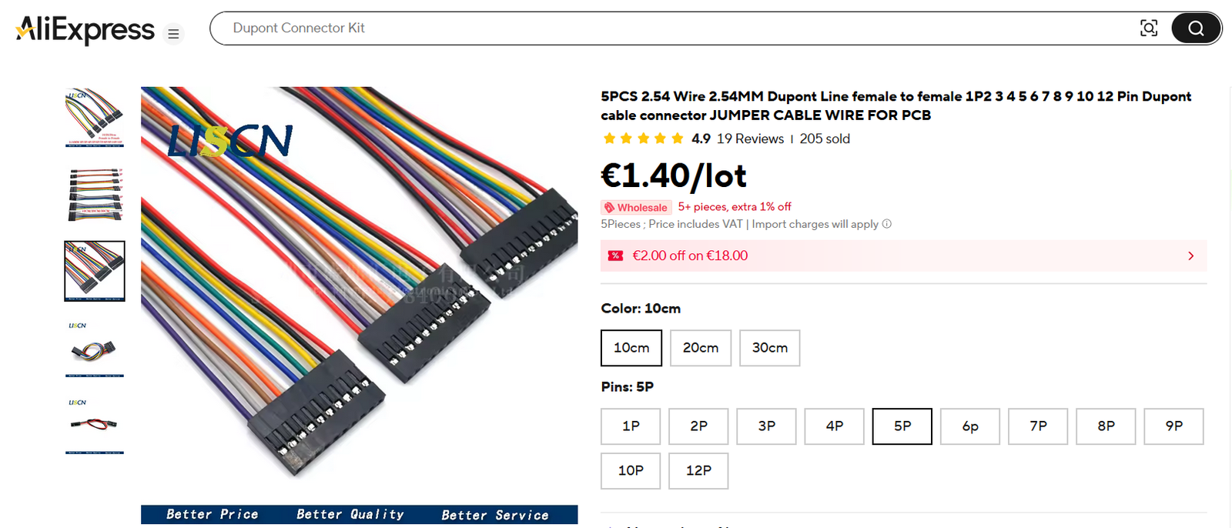
images/parts/AE_dupont_5p.png
