om7ea/B737/images/parts/AE_encoder.png

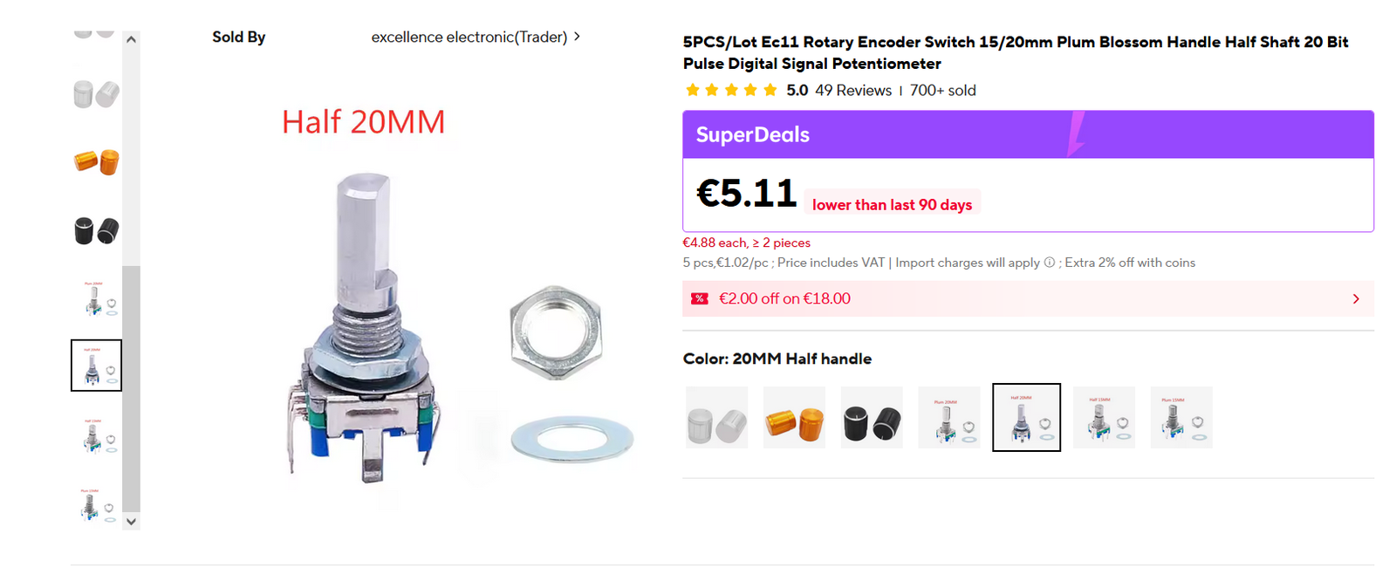
images/parts/AE_encoder.png
