om7ea/B737/images/parts/AE_i2c_module.png

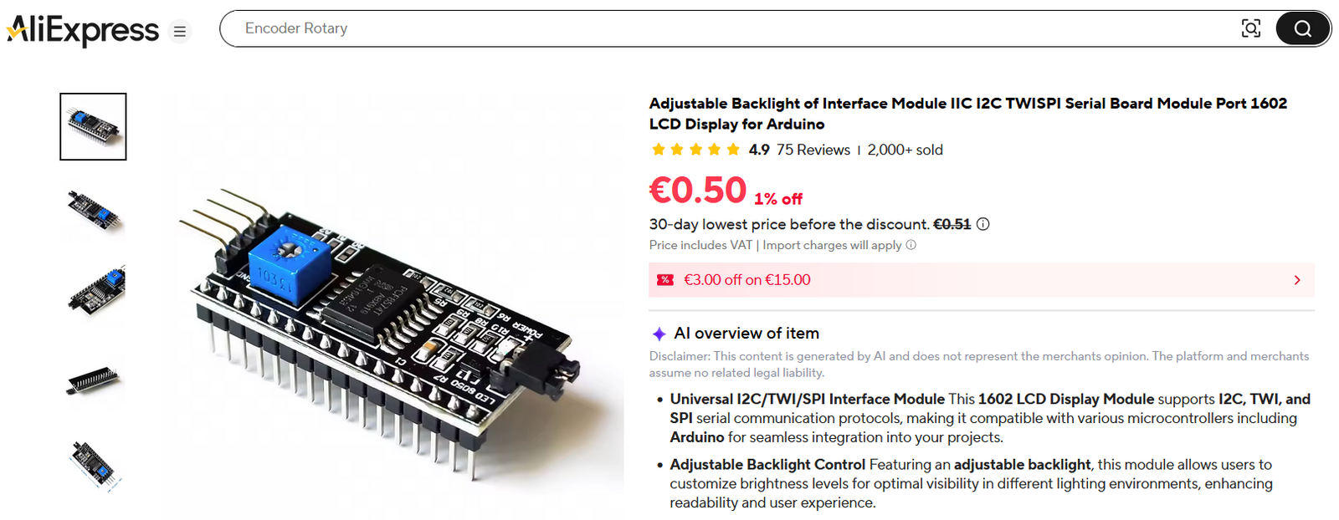
images/parts/AE_i2c_module.png
