om7ea/B737/images/parts/AE_KF301.png

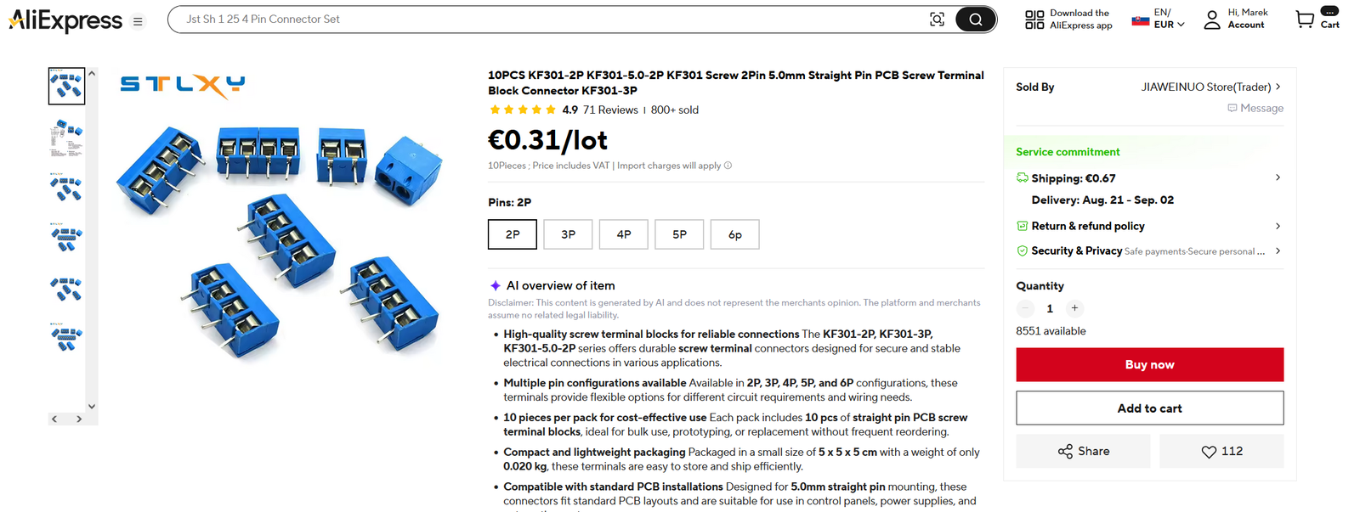
images/parts/AE_KF301.png
