om7ea/B737/images/parts/AE_lcd_1601.png

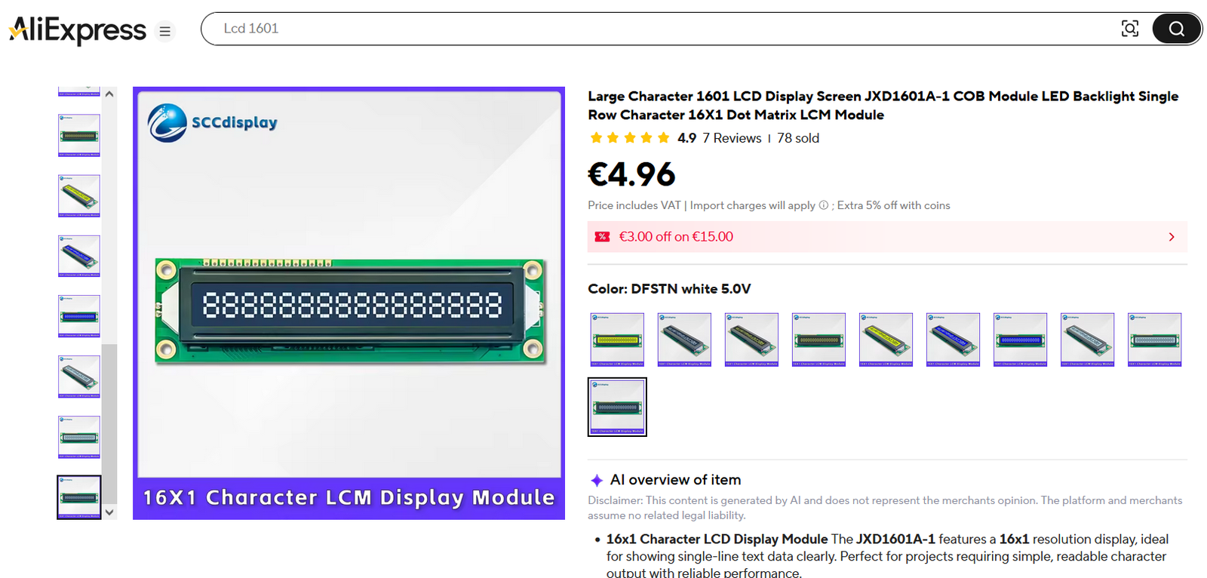
images/parts/AE_lcd_1601.png
