om7ea/B737/images/parts/AE_led_green.png

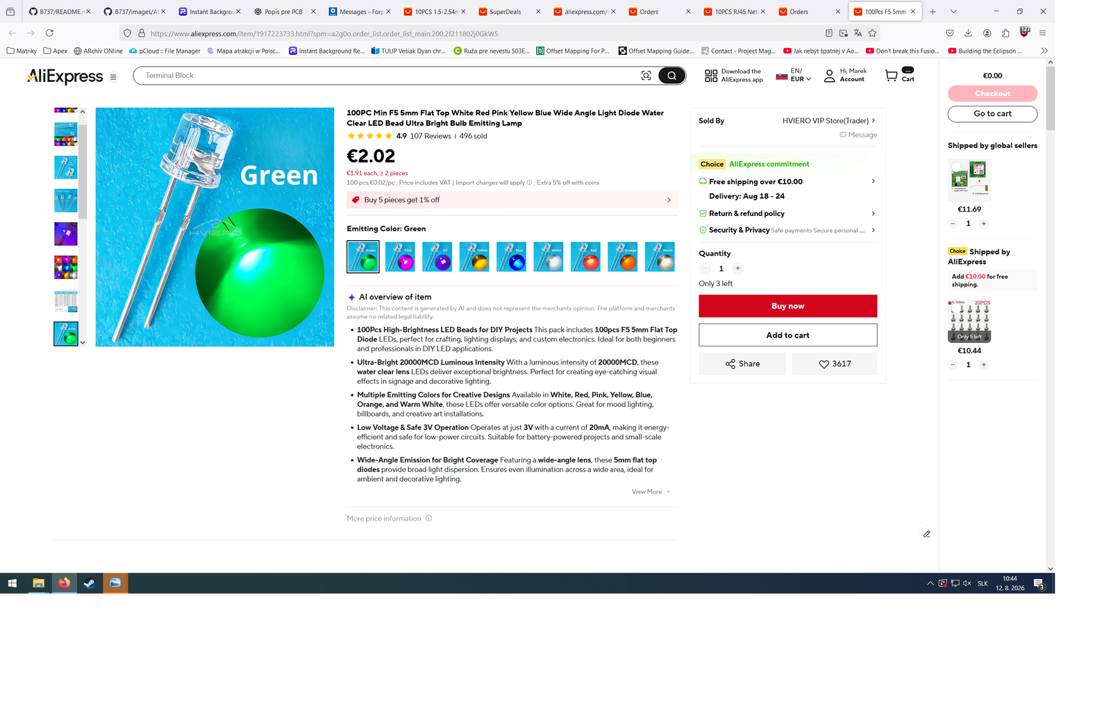
images/parts/AE_led_green.png
