om7ea/B737/images/parts/AE_led_strip.png

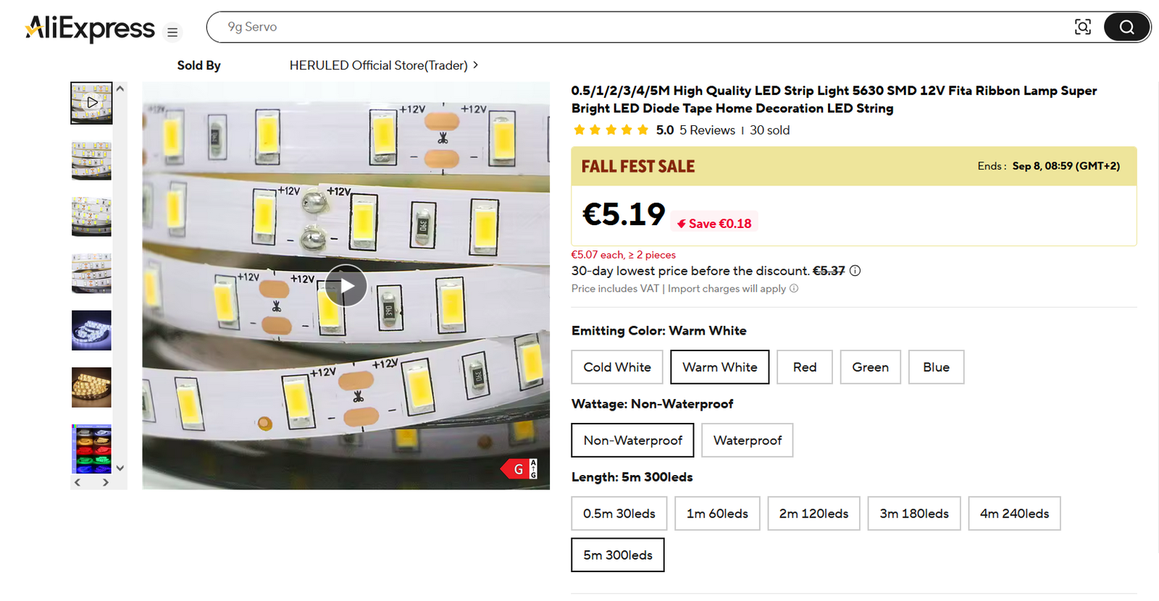
images/parts/AE_led_strip.png
