om7ea/B737/images/parts/AE_led_white.png

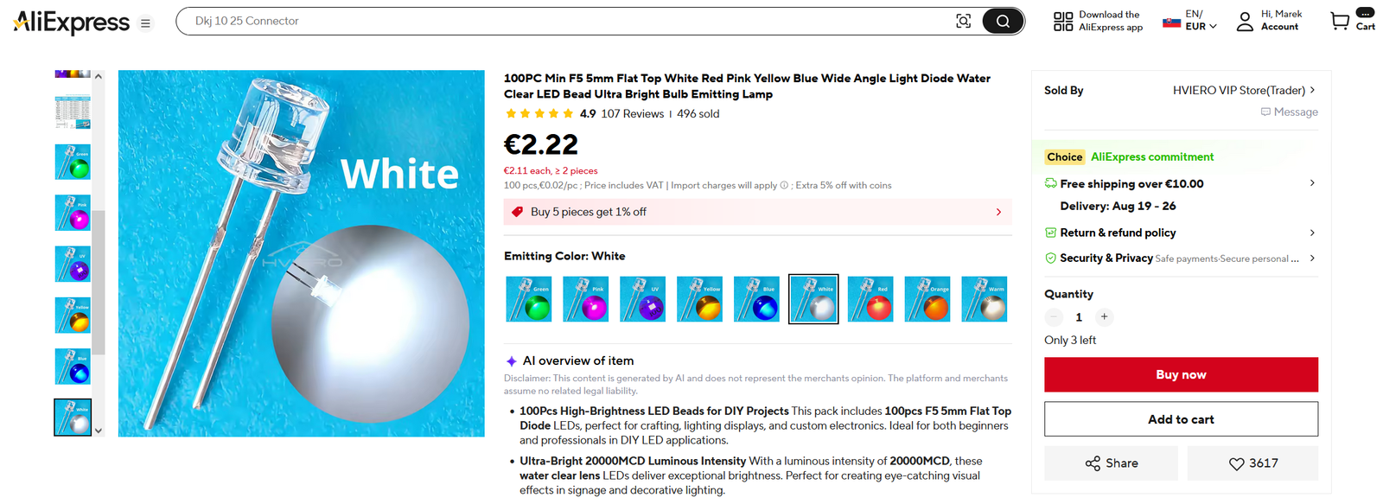
images/parts/AE_led_white.png
