om7ea/B737/images/parts/AE_led_yellow.png

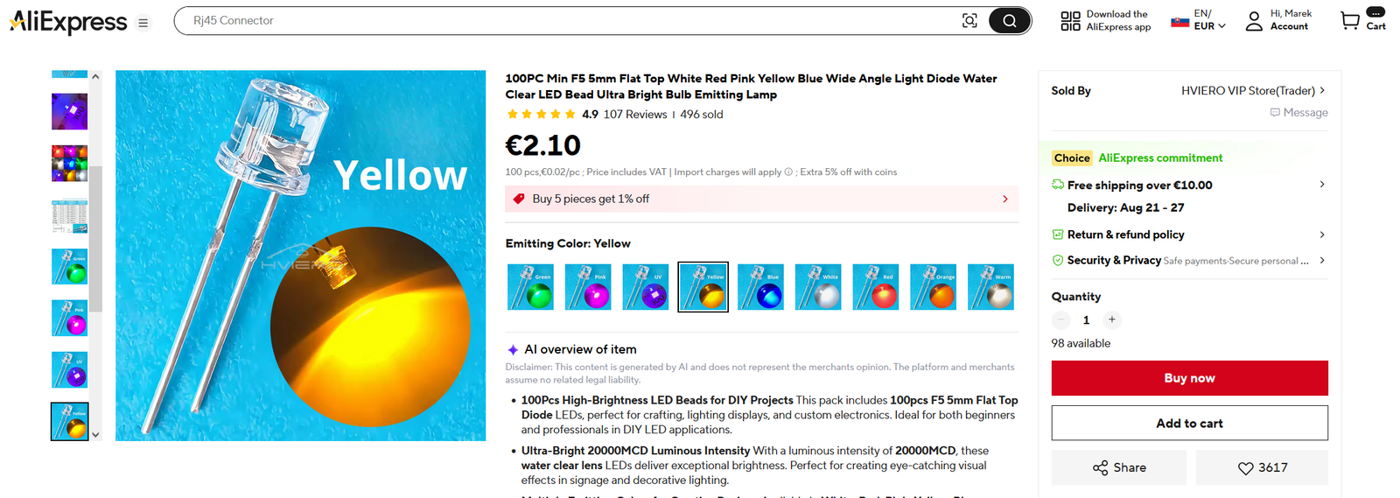
images/parts/AE_led_yellow.png
