om7ea/B737/images/parts/AE_MAX7219.png

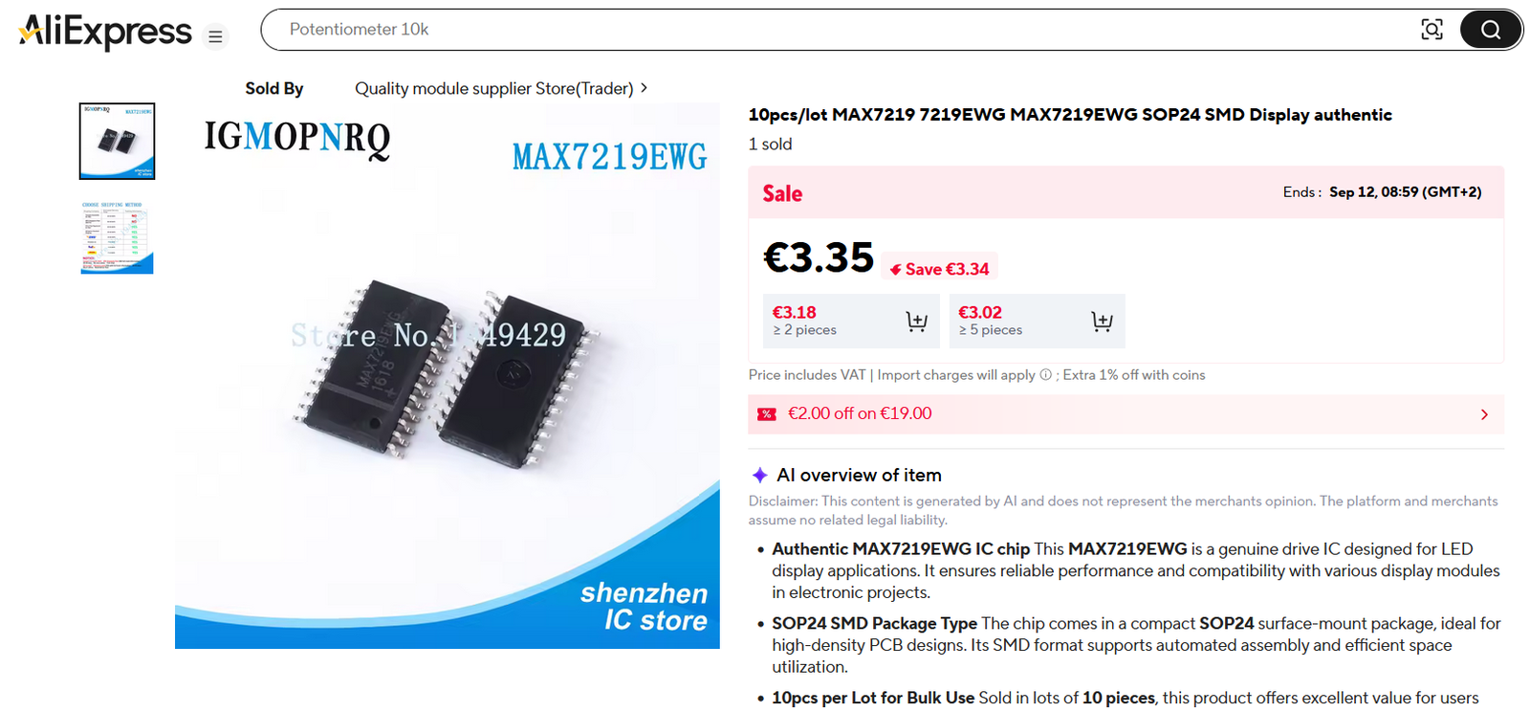
images/parts/AE_MAX7219.png
