om7ea/B737/images/parts/AE_mega.png

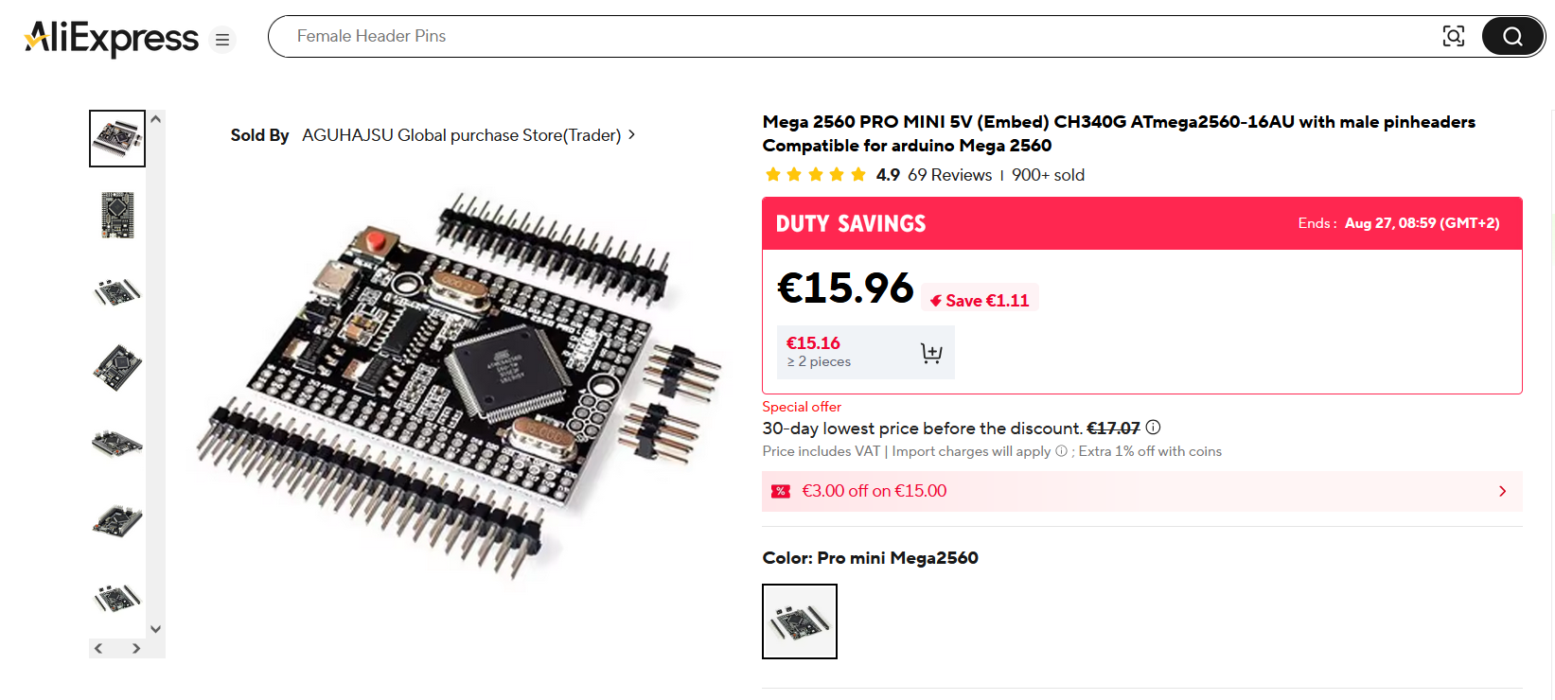
images/parts/AE_mega.png
