om7ea/B737/images/parts/AE_plug_male.png

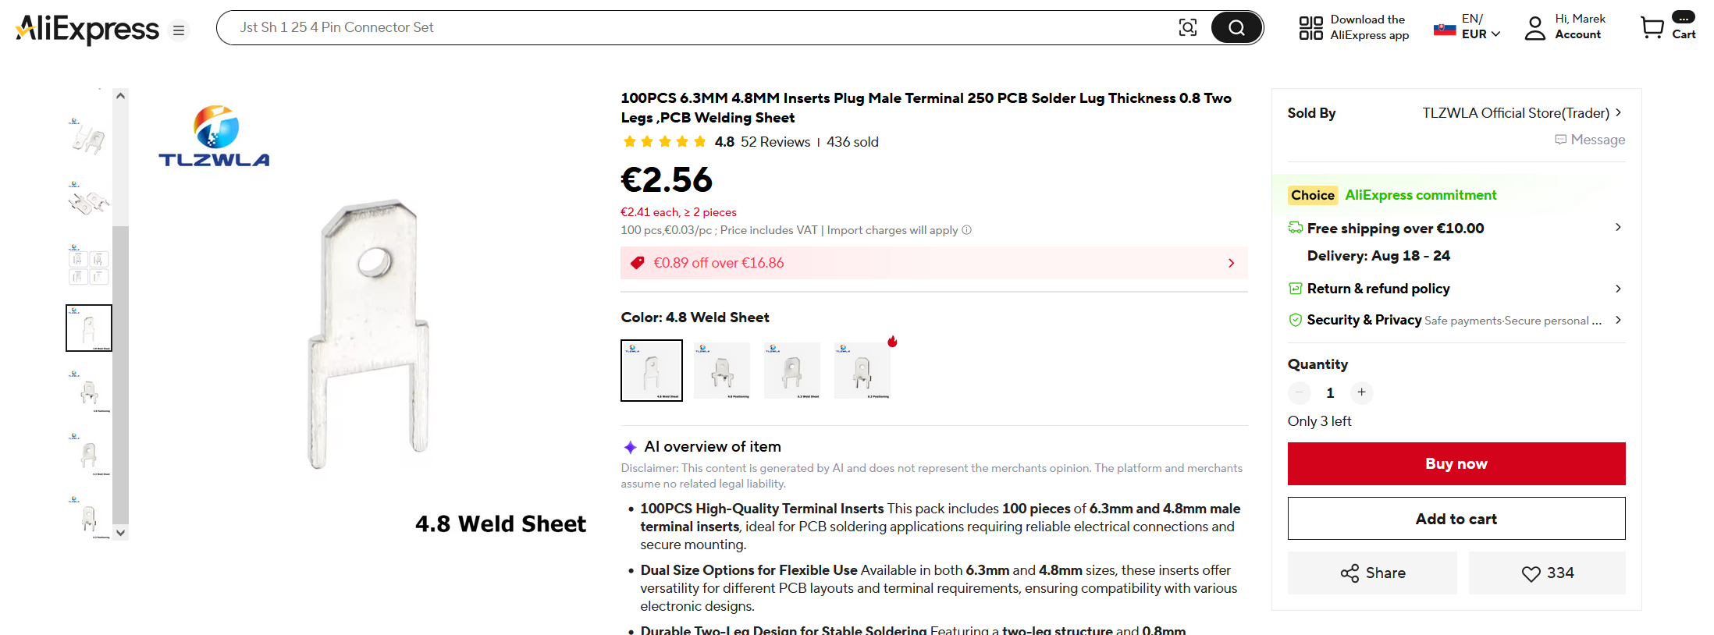
images/parts/AE_plug_male.png
