om7ea/B737/images/parts/AE_potentiometer.png

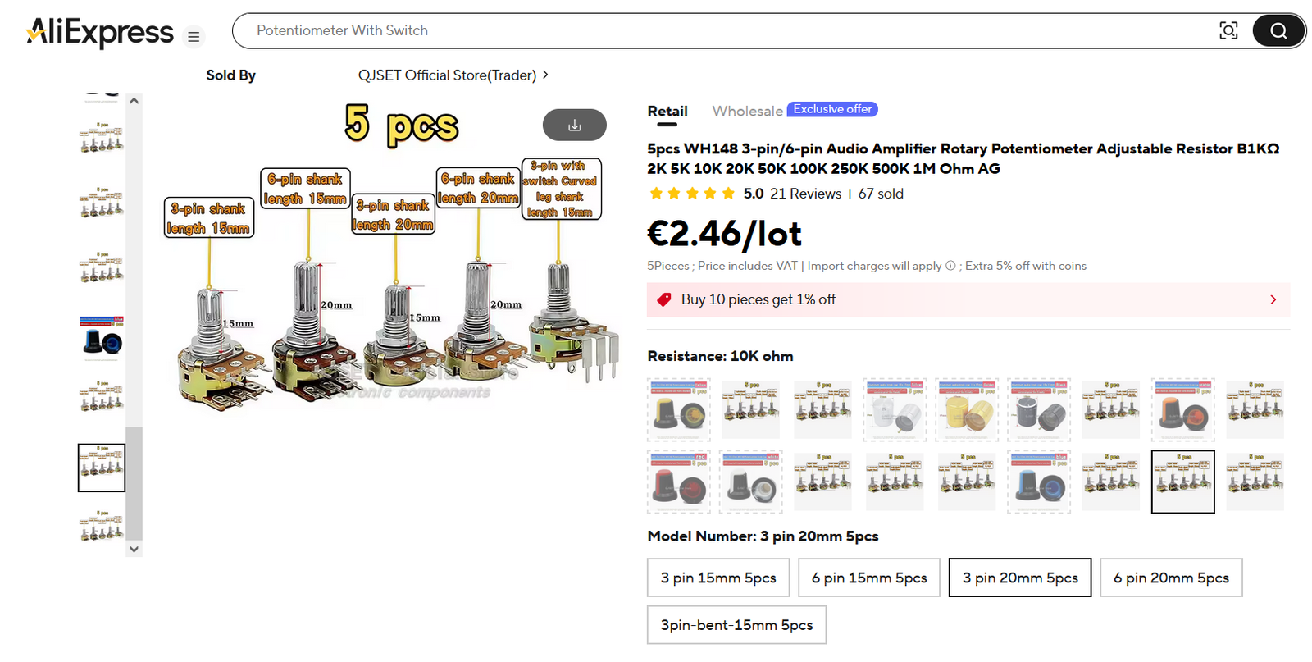
images/parts/AE_potentiometer.png
