om7ea/B737/images/parts/AE_RJ45.png

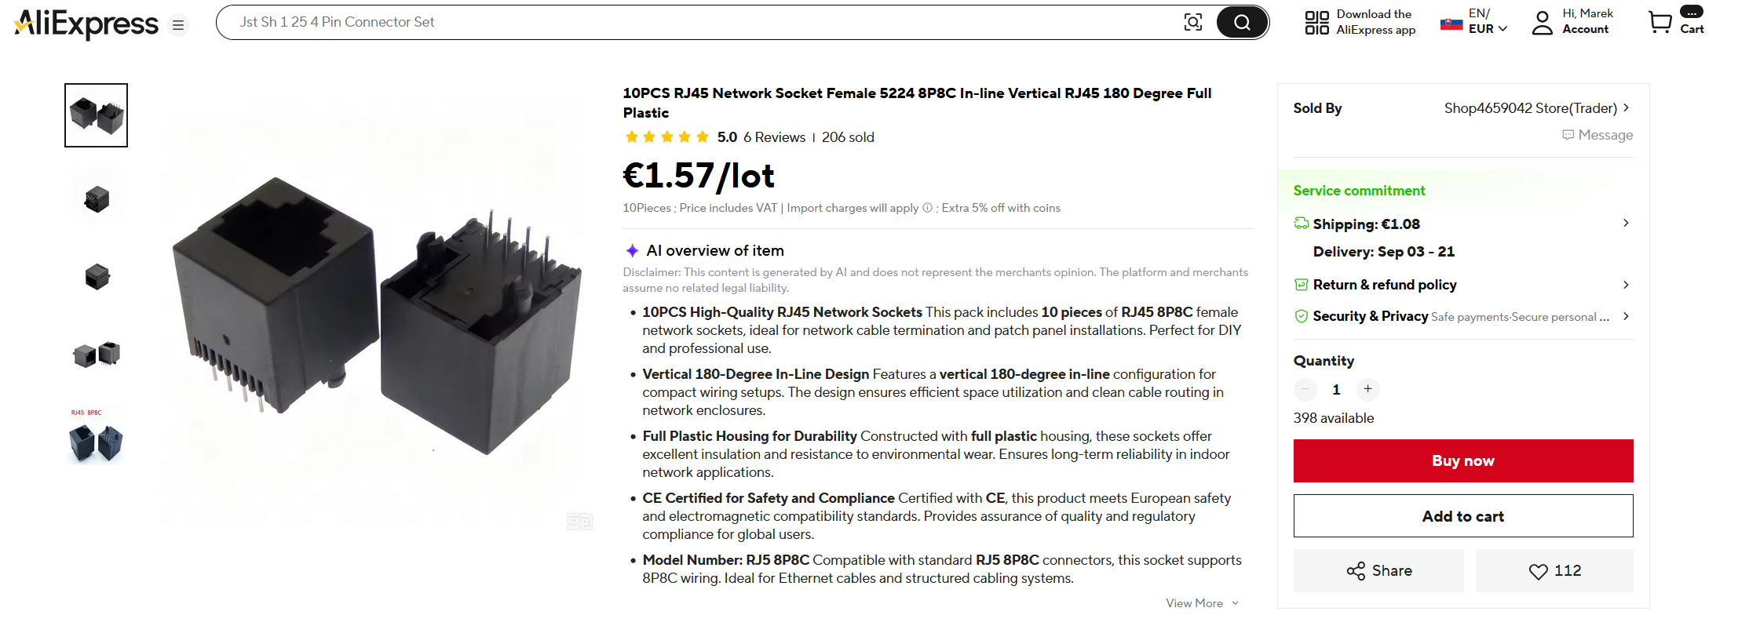
images/parts/AE_RJ45.png
