om7ea/B737/images/parts/AE_servo_MG90S.png

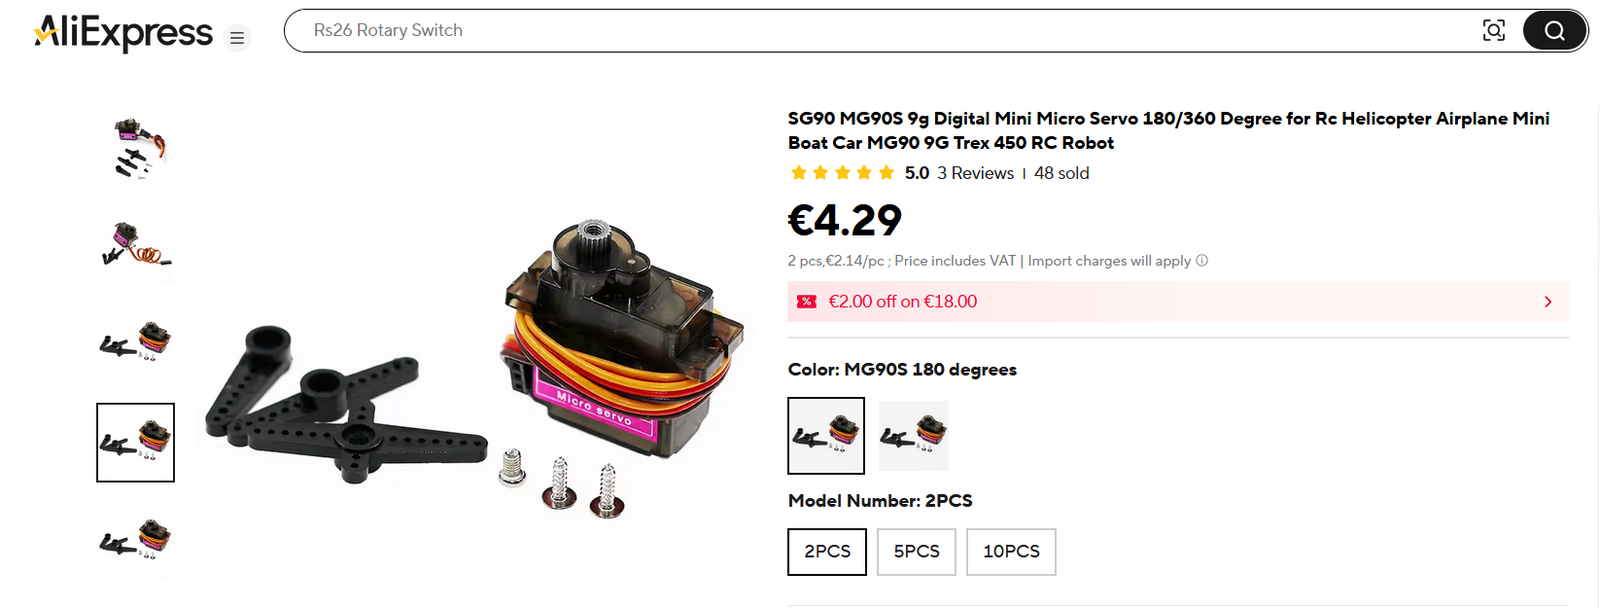
images/parts/AE_servo_MG90S.png
