om7ea/B737/images/parts/AE_servo_SG90.png

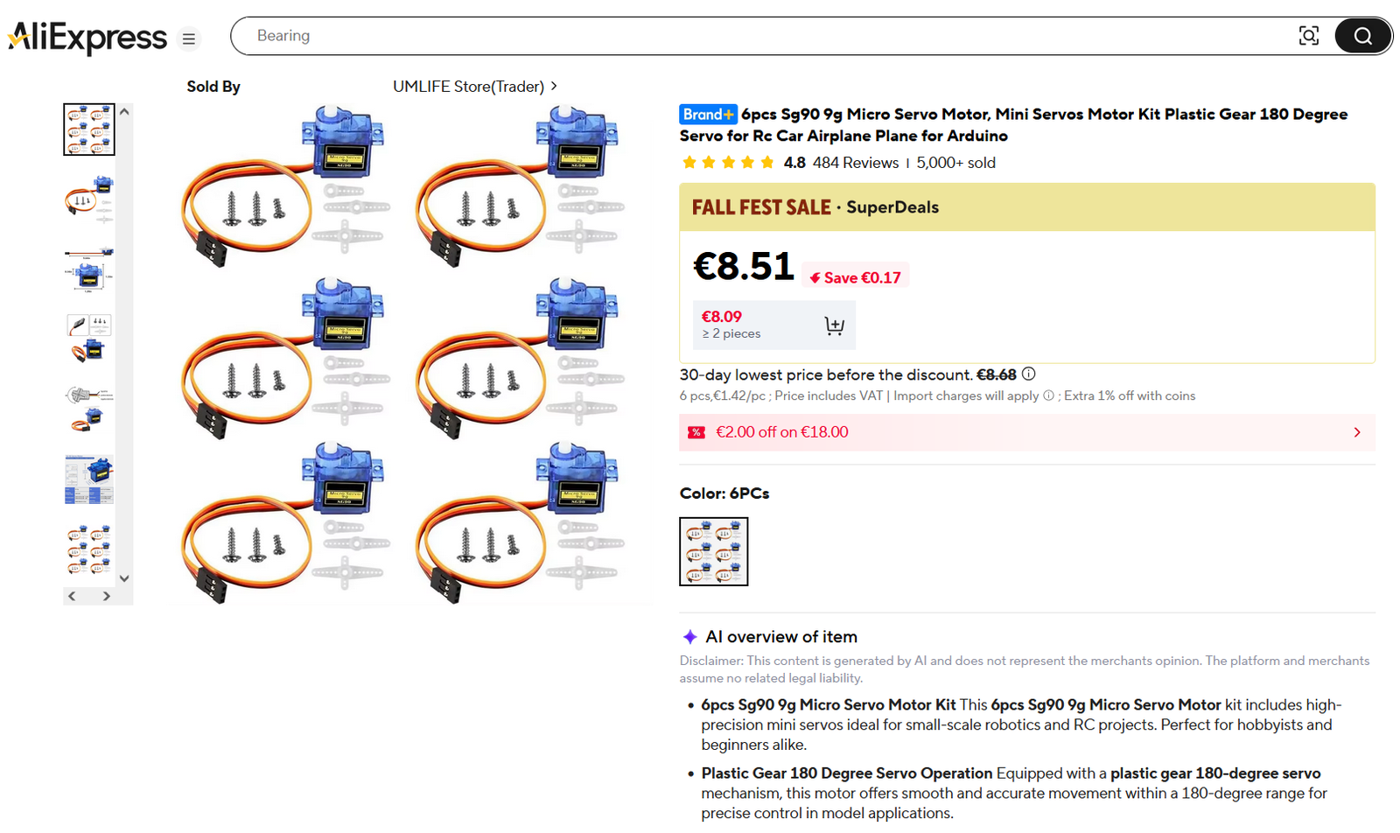
images/parts/AE_servo_SG90.png
