om7ea/B737/images/parts/AE_socket_2x21.png

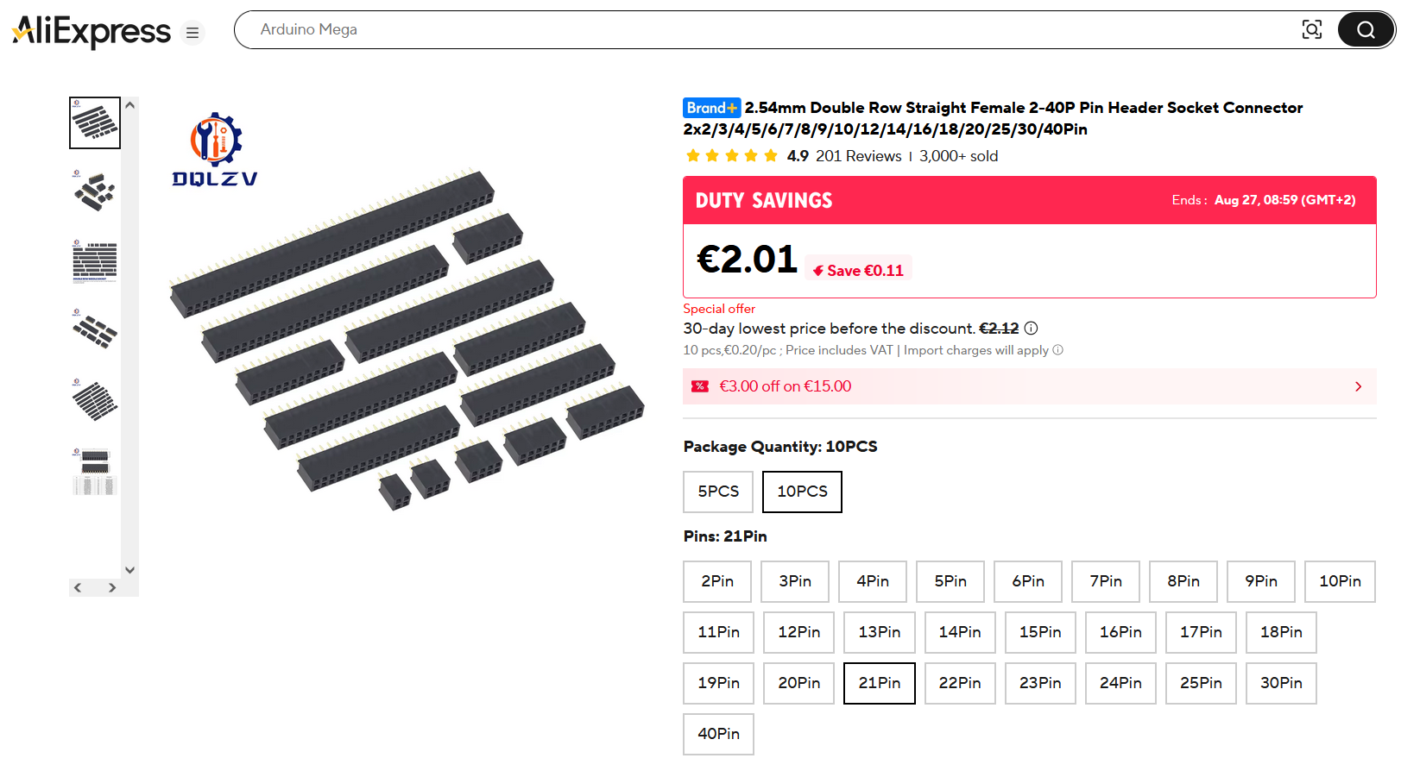
images/parts/AE_socket_2x21.png
