om7ea/B737/images/parts/AE_splice_F15.png

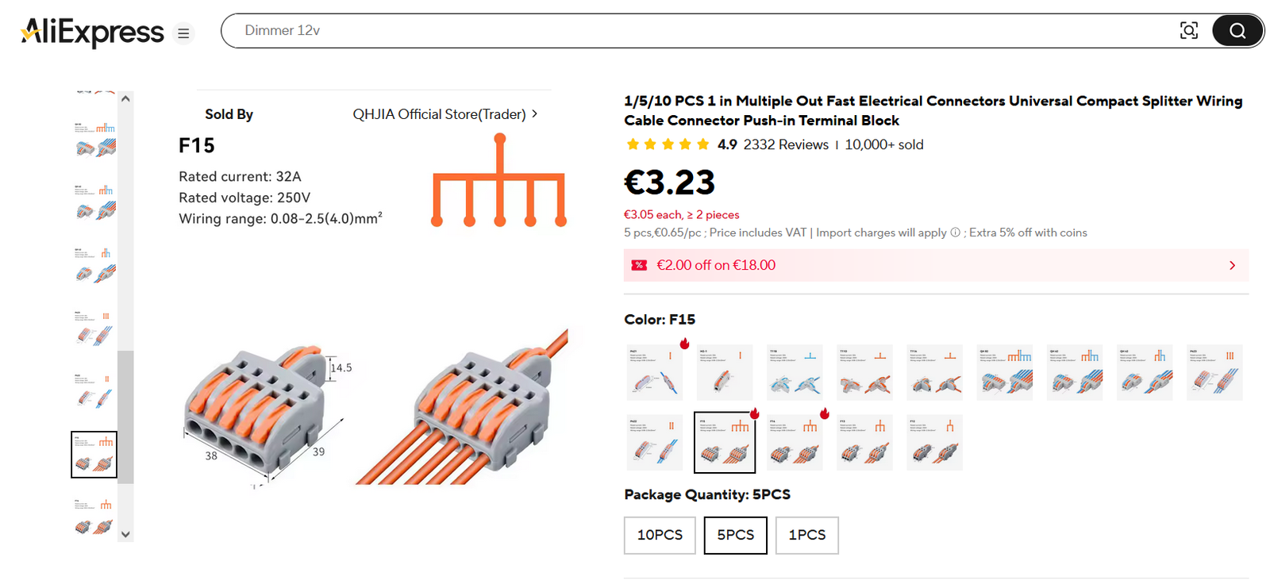
images/parts/AE_splice_F15.png
