om7ea/B737/images/parts/AE_ULN2803.png

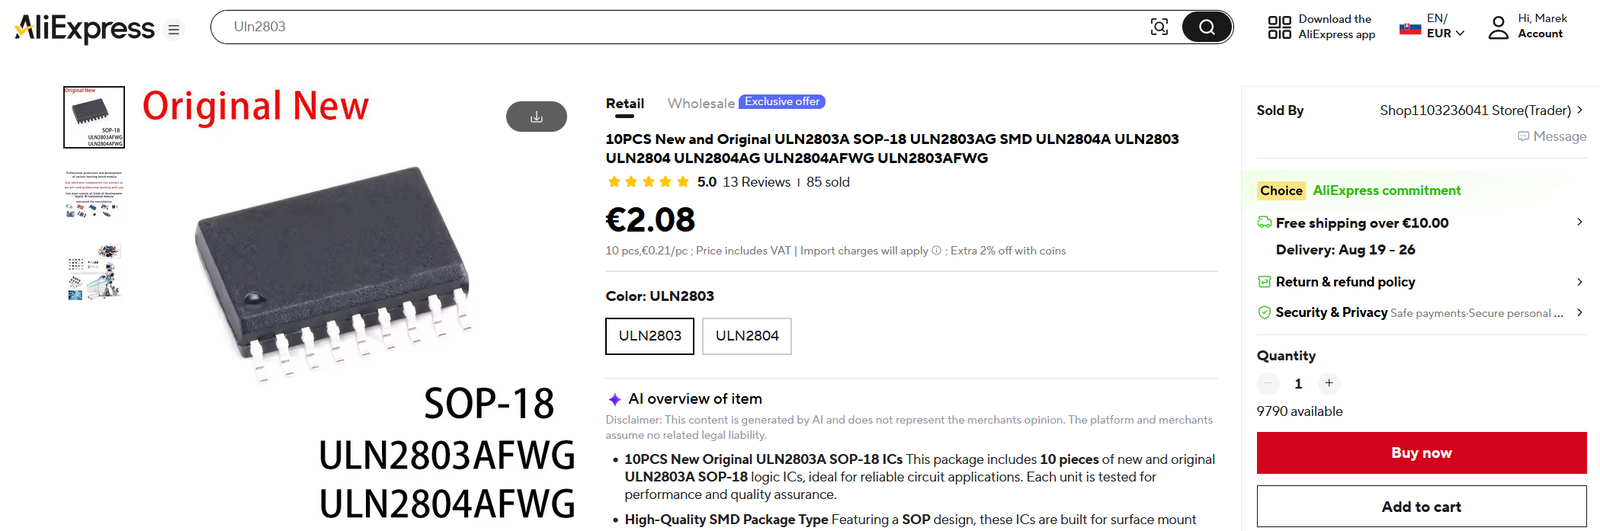
images/parts/AE_ULN2803.png
