om7ea/B737/images/parts/AE_usb_cable.png

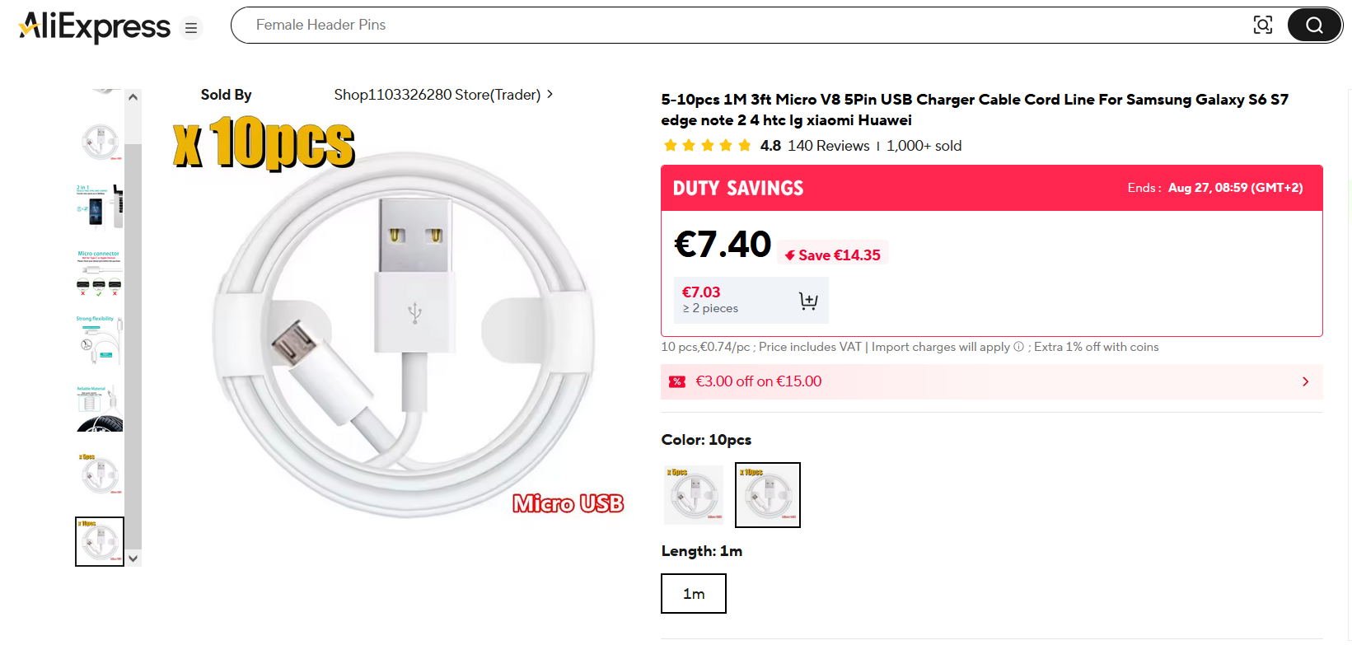
images/parts/AE_usb_cable.png
