om7ea/B737/images/parts/AE_usb_hub.png

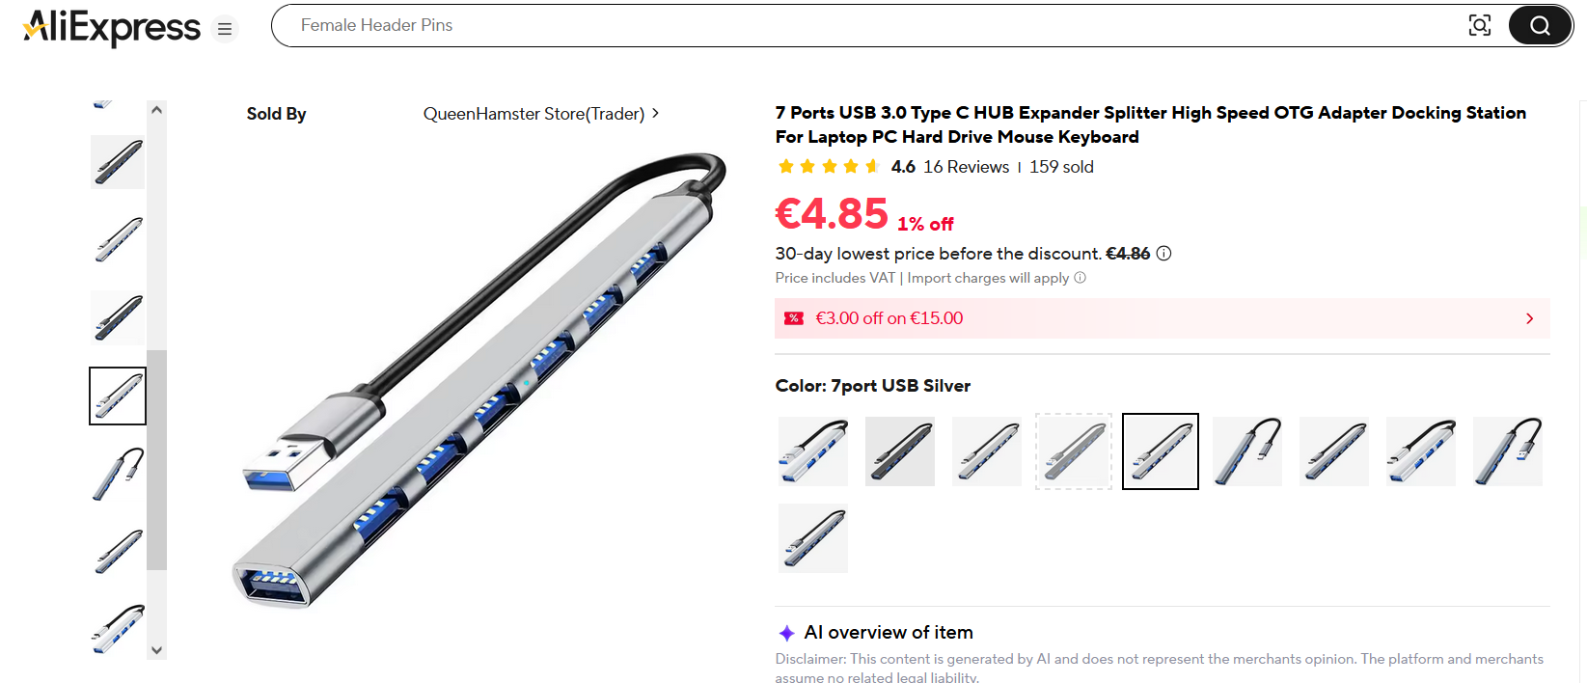
images/parts/AE_usb_hub.png
